carlosgj94/rapid-reader/crates/domain/src/reader.rs

extern crate alloc;

use alloc::boxed::Box;

use crate::{
    content::{
        ArticleId, CONTENT_ID_MAX_BYTES, CONTENT_TITLE_MAX_BYTES, CollectionKind,
        PrepareContentProgress, REMOTE_ITEM_ID_MAX_BYTES, ReaderPauseDetail, ReadingProgressEntry,
        SOURCE_ID_MAX_BYTES,
    },
    formatter::{MAX_PARAGRAPH_PREVIEW_BYTES, ReadingDocument, ReadingUnit},
    settings::{DEFAULT_READING_SPEED_WPM, MIN_READING_SPEED_WPM, READING_SPEED_STEP_WPM},
    text::InlineText,
};

pub const READER_WINDOW_MAX_UNITS: usize = 128;
const READER_WINDOW_OVERLAP_UNITS: u32 = 32;
const READER_WINDOW_PREFETCH_THRESHOLD_UNITS: u32 = 24;
const SPEED_RAMP_DURATION_MS: u64 = 10_000;
const SPEED_RAMP_START_NUMERATOR: u16 = 2;
const SPEED_RAMP_START_DENOMINATOR: u16 = 3;
const SPEED_RAMP_IDLE_AT_MS: u64 = u64::MAX;
const SPEED_RAMP_PENDING_AT_MS: u64 = u64::MAX - 1;
const PREPARE_PROGRESS_PERMILLE_MAX: u16 = 1_000;
const PREPARE_PROGRESS_ANIMATION_MIN_STEP_PERMILLE: u16 = 28;
const PREPARE_PROGRESS_STRIPE_PHASES: u8 = 8;

const EMPTY_READER_WINDOW: ReaderWindow = ReaderWindow::empty();

#[derive(Debug, Clone, Copy, Eq, PartialEq, Default)]
pub enum ReaderMode {
    #[default]
    Normal,
    Chat,
    Paused,
    ParagraphNavigation,
    LoadingContent,
}

#[derive(Debug, Clone, Copy, Eq, PartialEq, Default)]
pub enum PauseMenuRow {
    #[default]
    ResumeRsvp,
    ParagraphView,
    SaveArticle,
    Subscription,
}

impl PauseMenuRow {
    pub fn previous(self) -> Self {
        match self {
            Self::ResumeRsvp => Self::ResumeRsvp,
            Self::ParagraphView => Self::ResumeRsvp,
            Self::SaveArticle => Self::ParagraphView,
            Self::Subscription => Self::SaveArticle,
        }
    }

    pub fn next(self) -> Self {
        match self {
            Self::ResumeRsvp => Self::ParagraphView,
            Self::ParagraphView => Self::SaveArticle,
            Self::SaveArticle => Self::Subscription,
            Self::Subscription => Self::Subscription,
        }
    }
}

#[derive(Debug, Clone, Copy, Eq, PartialEq, Default)]
pub enum ReaderPauseMetadataStatus {
    #[default]
    Uninitialized,
    Loading,
    Ready,
    Failed,
}

#[derive(Debug, Clone, Copy, Eq, PartialEq, Default)]
pub enum ReaderPausePendingAction {
    #[default]
    None,
    Save,
    Subscription,
}

#[derive(Debug, Clone, Copy, Eq, PartialEq, Default)]
pub enum ReaderPauseActionError {
    #[default]
    None,
    Save,
    Subscription,
}

#[derive(Debug, Clone, Copy, Eq, PartialEq)]
pub enum ReaderPauseActionKind {
    Save,
    Subscription,
}

#[derive(Debug, Clone, Copy, Eq, PartialEq)]
pub struct ReaderPauseState {
    pub selected_row: PauseMenuRow,
    pub metadata_status: ReaderPauseMetadataStatus,
    pub pending_action: ReaderPausePendingAction,
    pub action_error: ReaderPauseActionError,
    pub is_saved: bool,
    pub is_subscribed_source: bool,
    pub saved_content_id: InlineText<REMOTE_ITEM_ID_MAX_BYTES>,
    pub source_id: InlineText<SOURCE_ID_MAX_BYTES>,
}

impl ReaderPauseState {
    pub const fn new() -> Self {
        Self {
            selected_row: PauseMenuRow::ResumeRsvp,
            metadata_status: ReaderPauseMetadataStatus::Uninitialized,
            pending_action: ReaderPausePendingAction::None,
            action_error: ReaderPauseActionError::None,
            is_saved: false,
            is_subscribed_source: false,
            saved_content_id: InlineText::new(),
            source_id: InlineText::new(),
        }
    }

    pub fn clear(&mut self) {
        *self = Self::new();
    }
}

impl Default for ReaderPauseState {
    fn default() -> Self {
        Self::new()
    }
}

#[derive(Debug, Clone, Copy, Eq, PartialEq, Default)]
pub struct ReaderProgress {
    pub unit_index: u32,
    pub paragraph_index: u16,
    pub total_paragraphs: u16,
    pub completion_percent: u8,
}

#[derive(Debug, Clone, Copy, Eq, PartialEq, Default)]
pub struct ReaderParagraphInfo {
    pub start_unit_index: u32,
    pub preview: InlineText<MAX_PARAGRAPH_PREVIEW_BYTES>,
}

#[derive(Debug, Clone, Eq, PartialEq)]
pub struct ReaderWindow {
    pub start_unit_index: u32,
    pub unit_count: u16,
    pub units: [ReadingUnit; READER_WINDOW_MAX_UNITS],
}

#[derive(Debug, Clone, Copy, Eq, PartialEq)]
pub struct ReaderWindowLoadRequest {
    pub content_id: InlineText<CONTENT_ID_MAX_BYTES>,
    pub window_start_unit_index: u32,
}

#[derive(Debug, Clone, Copy, Eq, PartialEq, Default)]
pub struct ReaderAdvanceOutcome {
    pub advanced: bool,
    pub load_request: Option<ReaderWindowLoadRequest>,
}

#[derive(Debug, Clone)]
pub struct ReaderSession {
    pub active_article: ArticleId,
    pub active_collection: CollectionKind,
    pub active_content_id: InlineText<CONTENT_ID_MAX_BYTES>,
    pub active_remote_revision: u64,
    pub title: InlineText<CONTENT_TITLE_MAX_BYTES>,
    active_window: Option<Box<ReaderWindow>>,
    prefetched_window: Option<Box<ReaderWindow>>,
    paragraphs: Option<Box<[ReaderParagraphInfo]>>,
    total_units: u32,
    pending_window_start_unit_index: Option<u32>,
    pending_seek_unit_index: Option<u32>,
    pub progress: ReaderProgress,
    pub mode: ReaderMode,
    pub resume_mode: ReaderMode,
    pub chat_available: bool,
    pub next_due_at_ms: Option<u64>,
    pub effective_wpm: u16,
    pub pause: ReaderPauseState,
    speed_ramp_start_wpm: u16,
    speed_ramp_started_at_ms: u64,
    prepare_progress: PrepareContentProgress,
    prepare_display_progress_permille: u16,
    prepare_stripe_phase: u8,
}

impl ReaderWindow {
    pub const fn empty() -> Self {
        Self {
            start_unit_index: 0,
            unit_count: 0,
            units: [ReadingUnit::new(); READER_WINDOW_MAX_UNITS],
        }
    }

    pub const fn is_empty(&self) -> bool {
        self.unit_count == 0
    }

    pub fn contains(&self, global_unit_index: u32) -> bool {
        !self.is_empty()
            && global_unit_index >= self.start_unit_index
            && global_unit_index < self.start_unit_index.saturating_add(self.unit_count as u32)
    }

    pub fn unit_at(&self, global_unit_index: u32) -> &ReadingUnit {
        if self.is_empty() {
            return &self.units[0];
        }

        let relative = global_unit_index
            .saturating_sub(self.start_unit_index)
            .min(self.unit_count.saturating_sub(1) as u32) as usize;
        &self.units[relative]
    }
}

impl ReaderSession {
    pub fn new() -> Self {
        Self {
            active_article: ArticleId(102),
            active_collection: CollectionKind::Saved,
            active_content_id: InlineText::new(),
            active_remote_revision: 0,
            title: InlineText::new(),
            active_window: None,
            prefetched_window: None,
            paragraphs: None,
            total_units: 0,
            pending_window_start_unit_index: None,
            pending_seek_unit_index: None,
            progress: ReaderProgress {
                unit_index: 0,
                paragraph_index: 1,
                total_paragraphs: 1,
                completion_percent: 0,
            },
            mode: ReaderMode::Normal,
            resume_mode: ReaderMode::Normal,
            chat_available: true,
            next_due_at_ms: None,
            effective_wpm: DEFAULT_READING_SPEED_WPM,
            pause: ReaderPauseState::new(),
            speed_ramp_start_wpm: 0,
            speed_ramp_started_at_ms: SPEED_RAMP_IDLE_AT_MS,
            prepare_progress: PrepareContentProgress::connecting(),
            prepare_display_progress_permille: 0,
            prepare_stripe_phase: 0,
        }
    }

    pub fn begin_content_loading(
        &mut self,
        collection: CollectionKind,
        content_id: InlineText<CONTENT_ID_MAX_BYTES>,
        title: InlineText<CONTENT_TITLE_MAX_BYTES>,
    ) {
        self.active_collection = collection;
        self.active_content_id = content_id;
        self.active_remote_revision = 0;
        self.title = title;
        self.active_window = None;
        self.prefetched_window = None;
        self.paragraphs = None;
        self.total_units = 0;
        self.pending_window_start_unit_index = None;
        self.pending_seek_unit_index = None;
        self.progress = ReaderProgress {
            unit_index: 0,
            paragraph_index: 1,
            total_paragraphs: 1,
            completion_percent: 0,
        };
        self.mode = ReaderMode::LoadingContent;
        self.resume_mode = ReaderMode::Normal;
        self.chat_available = false;
        self.next_due_at_ms = None;
        self.prepare_progress = PrepareContentProgress::connecting();
        self.prepare_display_progress_permille = 0;
        self.prepare_stripe_phase = 0;
        self.pause.clear();
        self.clear_speed_ramp();
        self.effective_wpm = DEFAULT_READING_SPEED_WPM;
    }

    pub fn open_article(
        &mut self,
        collection: CollectionKind,
        article: ArticleId,
        title: InlineText<CONTENT_TITLE_MAX_BYTES>,
        document: Box<ReadingDocument>,
        chat_available: bool,
        target_wpm: u16,
    ) {
        let paragraph_count = document.paragraph_count as usize;
        let mut paragraphs = alloc::vec::Vec::with_capacity(paragraph_count);
        let mut paragraph_index = 0usize;
        while paragraph_index < paragraph_count {
            paragraphs.push(ReaderParagraphInfo {
                start_unit_index: document.paragraphs[paragraph_index].start_unit_index as u32,
                preview: document.paragraphs[paragraph_index].preview,
            });
            paragraph_index += 1;
        }

        let mut window = Box::new(ReaderWindow::empty());
        let unit_count = document.unit_count.min(READER_WINDOW_MAX_UNITS as u16);
        let mut unit_index = 0usize;
        while unit_index < unit_count as usize {
            window.units[unit_index] = document.units[unit_index];
            unit_index += 1;
        }
        window.unit_count = unit_count;

        let _ = self.open_cached_reader_content(
            collection,
            article,
            InlineText::new(),
            0,
            title,
            document.unit_count as u32,
            paragraphs.into_boxed_slice(),
            window,
            chat_available,
            target_wpm,
            None,
        );
    }

    #[allow(clippy::too_many_arguments)]
    pub fn open_cached_reader_content(
        &mut self,
        collection: CollectionKind,
        article: ArticleId,
        content_id: InlineText<CONTENT_ID_MAX_BYTES>,
        remote_revision: u64,
        title: InlineText<CONTENT_TITLE_MAX_BYTES>,
        total_units: u32,
        paragraphs: Box<[ReaderParagraphInfo]>,
        window: Box<ReaderWindow>,
        chat_available: bool,
        target_wpm: u16,
        resume_paragraph_index: Option<u16>,
    ) -> Option<ReaderWindowLoadRequest> {
        self.active_collection = collection;
        self.active_article = article;
        self.active_content_id = content_id;
        self.active_remote_revision = remote_revision;
        self.title = title;
        self.total_units = total_units;
        self.paragraphs = Some(paragraphs);
        self.active_window = Some(window);
        self.prefetched_window = None;
        self.pending_window_start_unit_index = None;
        self.pending_seek_unit_index = None;
        self.progress.unit_index = 0;
        self.sync_progress();
        self.mode = ReaderMode::Normal;
        self.resume_mode = ReaderMode::Normal;
        self.chat_available = chat_available;
        self.next_due_at_ms = None;
        self.prepare_progress = PrepareContentProgress::connecting();
        self.prepare_display_progress_permille = 0;
        self.prepare_stripe_phase = 0;
        self.pause.clear();
        let request = resume_paragraph_index.and_then(|paragraph_index| {
            self.seek_to_unit(self.paragraph_start(paragraph_index.max(1)), target_wpm)
        });
        if self.pending_seek_unit_index.is_none() && self.progress.unit_index == 0 {
            self.arm_speed_ramp(target_wpm);
        }
        request
    }

    pub fn apply_loaded_window(&mut self, window: Box<ReaderWindow>) {
        let pending_seek = self.pending_seek_unit_index;
        self.pending_window_start_unit_index = None;

        if let Some(target_unit_index) = pending_seek
            && window.contains(target_unit_index)
        {
            Self::write_window_slot(&mut self.active_window, window);
            self.prefetched_window = None;
            self.pending_seek_unit_index = None;
            self.progress.unit_index = target_unit_index;
            self.sync_progress();
            self.next_due_at_ms = None;
            return;
        }

        let replace_active = self.active_window.as_ref().is_none_or(|active| {
            active.is_empty() || window.start_unit_index <= active.start_unit_index
        });

        if replace_active {
            Self::write_window_slot(&mut self.active_window, window);
            self.sync_progress();
        } else {
            Self::write_window_slot(&mut self.prefetched_window, window);
        }
    }

    pub fn unload_document(&mut self) {
        self.active_content_id = InlineText::new();
        self.active_remote_revision = 0;
        self.active_window = None;
        self.prefetched_window = None;
        self.paragraphs = None;
        self.total_units = 0;
        self.pending_window_start_unit_index = None;
        self.pending_seek_unit_index = None;
        self.progress = ReaderProgress {
            unit_index: 0,
            paragraph_index: 1,
            total_paragraphs: 1,
            completion_percent: 0,
        };
        self.mode = ReaderMode::Normal;
        self.resume_mode = ReaderMode::Normal;
        self.next_due_at_ms = None;
        self.clear_speed_ramp();
        self.effective_wpm = DEFAULT_READING_SPEED_WPM;
        self.prepare_progress = PrepareContentProgress::connecting();
        self.prepare_display_progress_permille = 0;
        self.prepare_stripe_phase = 0;
        self.pause.clear();
    }

    pub fn clear_pending_window_request(&mut self) {
        let had_pending_seek = self.pending_seek_unit_index.is_some();
        self.pending_window_start_unit_index = None;
        self.pending_seek_unit_index = None;
        self.prefetched_window = None;
        self.next_due_at_ms = None;
        if had_pending_seek {
            self.clear_speed_ramp();
        }
    }

    pub fn show_normal(&mut self) {
        if matches!(self.mode, ReaderMode::Normal | ReaderMode::Chat) {
            self.mode = ReaderMode::Normal;
            self.resume_mode = ReaderMode::Normal;
        }
    }

    pub fn show_chat(&mut self) {
        if self.chat_available && matches!(self.mode, ReaderMode::Normal | ReaderMode::Chat) {
            self.mode = ReaderMode::Chat;
            self.resume_mode = ReaderMode::Chat;
        }
    }

    pub fn pause(&mut self, seeded_is_saved: bool) {
        if matches!(self.mode, ReaderMode::Normal | ReaderMode::Chat) {
            self.resume_mode = self.mode;
            self.mode = ReaderMode::Paused;
            self.next_due_at_ms = None;
            self.clear_speed_ramp();
            self.pause.selected_row = PauseMenuRow::ResumeRsvp;
            if !matches!(self.pause.metadata_status, ReaderPauseMetadataStatus::Ready)
                && !matches!(self.pause.pending_action, ReaderPausePendingAction::Save)
            {
                self.pause.is_saved = seeded_is_saved;
            }
        }
    }

    pub fn resume(&mut self, target_wpm: u16) {
        if matches!(self.mode, ReaderMode::Paused) {
            self.mode = self.resume_mode;
            self.next_due_at_ms = None;
            self.arm_speed_ramp(target_wpm);
        }
    }

    pub fn open_paragraph_navigation(&mut self) {
        if matches!(self.mode, ReaderMode::Paused) {
            self.mode = ReaderMode::ParagraphNavigation;
            self.next_due_at_ms = None;
        }
    }

    pub fn close_paragraph_navigation(&mut self) {
        if matches!(self.mode, ReaderMode::ParagraphNavigation) {
            self.mode = ReaderMode::Paused;
        }
    }

    pub fn move_pause_selection(&mut self, previous: bool) {
        if !matches!(self.mode, ReaderMode::Paused) {
            return;
        }

        self.pause.selected_row = if previous {
            self.pause.selected_row.previous()
        } else {
            self.pause.selected_row.next()
        };
    }

    pub const fn selected_pause_row(&self) -> PauseMenuRow {
        self.pause.selected_row
    }

    pub const fn pause_needs_detail_load(&self) -> bool {
        matches!(self.mode, ReaderMode::Paused)
            && !self.active_content_id.is_empty()
            && matches!(
                self.pause.metadata_status,
                ReaderPauseMetadataStatus::Uninitialized | ReaderPauseMetadataStatus::Failed
            )
            && matches!(self.pause.pending_action, ReaderPausePendingAction::None)
    }

    pub fn begin_pause_detail_load(&mut self) {
        if self.active_content_id.is_empty() {
            return;
        }

        self.pause.metadata_status = ReaderPauseMetadataStatus::Loading;
        self.pause.action_error = ReaderPauseActionError::None;
    }

    pub fn apply_pause_detail(&mut self, detail: ReaderPauseDetail) {
        if self.active_content_id != detail.content_id {
            return;
        }

        self.pause.metadata_status = ReaderPauseMetadataStatus::Ready;
        self.pause.pending_action = ReaderPausePendingAction::None;
        self.pause.action_error = ReaderPauseActionError::None;
        self.pause.is_saved = detail.is_saved;
        self.pause.is_subscribed_source = detail.is_subscribed_source;
        self.pause.saved_content_id = detail.saved_content_id;
        self.pause.source_id = detail.source_id;
    }

    pub fn mark_pause_detail_failed(&mut self, content_id: InlineText<CONTENT_ID_MAX_BYTES>) {
        if self.active_content_id != content_id {
            return;
        }

        if !matches!(self.pause.pending_action, ReaderPausePendingAction::None) {
            return;
        }

        self.pause.metadata_status = ReaderPauseMetadataStatus::Failed;
    }

    pub fn begin_pause_save_toggle(&mut self) {
        self.pause.pending_action = ReaderPausePendingAction::Save;
        if matches!(self.pause.action_error, ReaderPauseActionError::Save) {
            self.pause.action_error = ReaderPauseActionError::None;
        }
    }

    pub fn begin_pause_subscription_toggle(&mut self) {
        self.pause.pending_action = ReaderPausePendingAction::Subscription;
        if matches!(
            self.pause.action_error,
            ReaderPauseActionError::Subscription
        ) {
            self.pause.action_error = ReaderPauseActionError::None;
        }
    }

    pub fn apply_pause_action(
        &mut self,
        content_id: InlineText<CONTENT_ID_MAX_BYTES>,
        action: ReaderPauseActionKind,
        enabled: bool,
    ) {
        if self.active_content_id != content_id {
            return;
        }

        match action {
            ReaderPauseActionKind::Save => {
                self.pause.pending_action = ReaderPausePendingAction::None;
                self.pause.action_error = ReaderPauseActionError::None;
                self.pause.is_saved = enabled;
            }
            ReaderPauseActionKind::Subscription => {
                self.pause.pending_action = ReaderPausePendingAction::None;
                self.pause.action_error = ReaderPauseActionError::None;
                self.pause.is_subscribed_source = enabled;
            }
        }
    }

    pub fn fail_pause_action(
        &mut self,
        content_id: InlineText<CONTENT_ID_MAX_BYTES>,
        action: ReaderPauseActionKind,
    ) {
        if self.active_content_id != content_id {
            return;
        }

        match action {
            ReaderPauseActionKind::Save => {
                self.pause.pending_action = ReaderPausePendingAction::None;
                self.pause.action_error = ReaderPauseActionError::Save;
            }
            ReaderPauseActionKind::Subscription => {
                self.pause.pending_action = ReaderPausePendingAction::None;
                self.pause.action_error = ReaderPauseActionError::Subscription;
            }
        }
    }

    pub fn commit_paragraph_navigation(
        &mut self,
        target_wpm: u16,
    ) -> Option<ReaderWindowLoadRequest> {
        if !matches!(self.mode, ReaderMode::ParagraphNavigation) {
            return None;
        }

        self.mode = self.resume_mode;
        self.seek_to_unit(
            self.paragraph_start(self.progress.paragraph_index),
            target_wpm,
        )
    }

    pub fn move_paragraph(&mut self, previous: bool) {
        let min_paragraph = 1u16;
        let max_paragraph = self.progress.total_paragraphs.max(1);

        self.progress.paragraph_index = if previous {
            self.progress
                .paragraph_index
                .saturating_sub(1)
                .max(min_paragraph)
        } else {
            self.progress
                .paragraph_index
                .saturating_add(1)
                .min(max_paragraph)
        };
    }

    pub fn jump_live_previous_paragraph(
        &mut self,
        target_wpm: u16,
    ) -> Option<ReaderWindowLoadRequest> {
        if !self.is_active_reading() {
            return None;
        }

        let current_start = self.paragraph_start(self.progress.paragraph_index);
        if self.progress.unit_index > current_start {
            return self.seek_to_unit(current_start, target_wpm);
        }

        if self.progress.paragraph_index > 1 {
            return self.seek_to_unit(
                self.paragraph_start(self.progress.paragraph_index - 1),
                target_wpm,
            );
        }

        None
    }

    pub fn jump_live_next_paragraph(&mut self, target_wpm: u16) -> Option<ReaderWindowLoadRequest> {
        if !self.is_active_reading()
            || self.progress.paragraph_index >= self.progress.total_paragraphs.max(1)
        {
            return None;
        }

        self.seek_to_unit(
            self.paragraph_start(self.progress.paragraph_index + 1),
            target_wpm,
        )
    }

    pub const fn is_active_reading(&self) -> bool {
        matches!(self.mode, ReaderMode::Normal | ReaderMode::Chat)
    }

    pub fn advance_if_due(&mut self, now_ms: u64, wpm: u16) -> ReaderAdvanceOutcome {
        let mut outcome = ReaderAdvanceOutcome::default();
        if !self.is_active_reading() || self.active_window().is_empty() {
            return outcome;
        }

        if self.pending_seek_unit_index.is_some() {
            return outcome;
        }

        self.refresh_effective_wpm(now_ms, wpm);
        let current = self.current_unit();
        let next_due = self
            .next_due_at_ms
            .unwrap_or_else(|| now_ms.saturating_add(current.dwell_ms(self.effective_wpm) as u64));

        if self.next_due_at_ms.is_none() {
            self.next_due_at_ms = Some(next_due);
            outcome.load_request = self.maybe_request_prefetch();
            return outcome;
        }

        if now_ms < next_due {
            outcome.load_request = self.maybe_request_prefetch();
            return outcome;
        }

        if self.progress.unit_index.saturating_add(1) >= self.total_units.max(1) {
            self.next_due_at_ms = None;
            self.progress.completion_percent = 100;
            self.clear_speed_ramp();
            self.effective_wpm = wpm;
            return outcome;
        }

        let next_unit_index = self.progress.unit_index.saturating_add(1);
        if !self.active_window().contains(next_unit_index) {
            if self
                .prefetched_window
                .as_ref()
                .is_some_and(|window| window.contains(next_unit_index))
            {
                self.active_window = self.prefetched_window.take();
            } else {
                self.next_due_at_ms = None;
                outcome.load_request =
                    self.load_request_for_window_start(self.window_start_for_unit(next_unit_index));
                return outcome;
            }
        }

        self.progress.unit_index = next_unit_index;
        self.sync_progress();
        self.refresh_effective_wpm(now_ms, wpm);
        self.next_due_at_ms =
            Some(now_ms.saturating_add(self.current_unit().dwell_ms(self.effective_wpm) as u64));
        outcome.advanced = true;
        outcome.load_request = self.maybe_request_prefetch();
        outcome
    }

    pub fn display_wpm(&self, target_wpm: u16) -> u16 {
        if self.speed_ramp_started_at_ms == SPEED_RAMP_IDLE_AT_MS {
            target_wpm
        } else {
            quantize_display_wpm(self.effective_wpm, target_wpm)
        }
    }

    pub const fn prepare_progress(&self) -> PrepareContentProgress {
        self.prepare_progress
    }

    pub fn update_prepare_progress(&mut self, progress: PrepareContentProgress) {
        if matches!(self.mode, ReaderMode::LoadingContent) {
            self.prepare_progress = progress;
            let target = prepare_progress_permille(progress);
            if target < self.prepare_display_progress_permille {
                self.prepare_display_progress_permille = target;
            }
        }
    }

    pub fn advance_prepare_animation(&mut self) {
        if !matches!(self.mode, ReaderMode::LoadingContent) {
            self.prepare_display_progress_permille =
                prepare_progress_permille(self.prepare_progress);
            self.prepare_stripe_phase = 0;
            return;
        }

        self.prepare_stripe_phase =
            (self.prepare_stripe_phase + 1) % PREPARE_PROGRESS_STRIPE_PHASES.max(1);

        let target = prepare_progress_permille(self.prepare_progress);
        if self.prepare_display_progress_permille >= target {
            self.prepare_display_progress_permille = target;
            return;
        }

        let delta = target.saturating_sub(self.prepare_display_progress_permille);
        let eased_step = delta / 3;
        let step = if eased_step > PREPARE_PROGRESS_ANIMATION_MIN_STEP_PERMILLE {
            eased_step
        } else {
            PREPARE_PROGRESS_ANIMATION_MIN_STEP_PERMILLE
        };
        self.prepare_display_progress_permille = self
            .prepare_display_progress_permille
            .saturating_add(step)
            .min(target);
    }

    pub const fn prepare_display_progress_width_px(&self, max_width_px: u16) -> u16 {
        ((max_width_px as u32 * self.prepare_display_progress_permille as u32)
            / PREPARE_PROGRESS_PERMILLE_MAX as u32) as u16
    }

    pub const fn prepare_stripe_phase(&self) -> u8 {
        self.prepare_stripe_phase
    }

    pub fn current_unit(&self) -> &ReadingUnit {
        self.active_window().unit_at(self.progress.unit_index)
    }

    pub fn reading_progress_checkpoint(&self) -> Option<ReadingProgressEntry> {
        if self.active_content_id.is_empty()
            || matches!(self.mode, ReaderMode::LoadingContent)
            || self.active_window().is_empty()
        {
            return None;
        }

        Some(
            ReadingProgressEntry {
                content_id: self.active_content_id,
                remote_revision: self.active_remote_revision,
                paragraph_index: self.progress.paragraph_index.max(1),
                total_paragraphs: self.progress.total_paragraphs.max(1),
            }
            .sanitized(),
        )
    }

    pub fn preview_for_paragraph(
        &self,
        paragraph_index: u16,
    ) -> InlineText<MAX_PARAGRAPH_PREVIEW_BYTES> {
        self.paragraphs
            .as_deref()
            .and_then(|paragraphs| {
                if paragraphs.is_empty() {
                    return None;
                }

                let safe_index = paragraph_index
                    .saturating_sub(1)
                    .min(paragraphs.len().saturating_sub(1) as u16)
                    as usize;
                Some(paragraphs[safe_index].preview)
            })
            .or_else(|| Self::preview_from_window(self.active_window(), paragraph_index))
            .or_else(|| {
                self.prefetched_window
                    .as_deref()
                    .and_then(|window| Self::preview_from_window(window, paragraph_index))
            })
            .unwrap_or_default()
    }

    pub fn paragraph_start(&self, paragraph_index: u16) -> u32 {
        let Some(paragraphs) = self.paragraphs.as_deref() else {
            return 0;
        };
        let safe_index = paragraph_index
            .saturating_sub(1)
            .min(paragraphs.len().saturating_sub(1) as u16) as usize;
        paragraphs[safe_index].start_unit_index
    }

    pub fn active_window(&self) -> &ReaderWindow {
        self.active_window
            .as_deref()
            .unwrap_or(&EMPTY_READER_WINDOW)
    }

    pub const fn progress_width_px(&self) -> u16 {
        ((400u32 * self.progress.completion_percent as u32) / 100u32) as u16
    }

    pub fn is_empty(&self) -> bool {
        self.total_units == 0 || self.active_window().is_empty()
    }

    fn sync_progress(&mut self) {
        let total_paragraphs = self
            .paragraphs
            .as_deref()
            .map(|paragraphs| paragraphs.len() as u16)
            .unwrap_or(0)
            .max(1);
        self.progress.total_paragraphs = total_paragraphs;
        self.progress.paragraph_index = self.find_paragraph_for_unit(self.progress.unit_index);

        let total_units = self.total_units.max(1);
        let current = self.progress.unit_index.min(total_units.saturating_sub(1)) + 1;
        self.progress.completion_percent = ((current * 100) / total_units) as u8;
    }

    fn find_paragraph_for_unit(&self, unit_index: u32) -> u16 {
        let Some(paragraphs) = self.paragraphs.as_deref() else {
            return 1;
        };
        if paragraphs.is_empty() {
            return 1;
        }

        let mut low = 0usize;
        let mut high = paragraphs.len();
        while low + 1 < high {
            let mid = (low + high) / 2;
            if paragraphs[mid].start_unit_index <= unit_index {
                low = mid;
            } else {
                high = mid;
            }
        }

        (low + 1) as u16
    }

    fn maybe_request_prefetch(&mut self) -> Option<ReaderWindowLoadRequest> {
        if self.active_content_id.is_empty()
            || self.prefetched_window.is_some()
            || self.pending_window_start_unit_index.is_some()
            || self.total_units == 0
        {
            return None;
        }

        let active = self.active_window();
        if active.is_empty() {
            return None;
        }

        let window_end = active
            .start_unit_index
            .saturating_add(active.unit_count as u32);
        if window_end >= self.total_units {
            return None;
        }

        let remaining_in_window =
            window_end.saturating_sub(self.progress.unit_index.saturating_add(1));
        if remaining_in_window > READER_WINDOW_PREFETCH_THRESHOLD_UNITS {
            return None;
        }

        let next_start = active
            .start_unit_index
            .saturating_add(active.unit_count as u32)
            .saturating_sub(READER_WINDOW_OVERLAP_UNITS);
        self.load_request_for_window_start(next_start)
    }

    fn load_request_for_window_start(
        &mut self,
        window_start_unit_index: u32,
    ) -> Option<ReaderWindowLoadRequest> {
        if self.active_content_id.is_empty() {
            return None;
        }

        let clamped_start = window_start_unit_index.min(self.total_units.saturating_sub(1));
        if self.pending_window_start_unit_index == Some(clamped_start)
            || self.active_window().start_unit_index == clamped_start
            || self
                .prefetched_window
                .as_ref()
                .is_some_and(|window| window.start_unit_index == clamped_start)
        {
            return None;
        }

        self.pending_window_start_unit_index = Some(clamped_start);
        Some(ReaderWindowLoadRequest {
            content_id: self.active_content_id,
            window_start_unit_index: clamped_start,
        })
    }

    fn seek_to_unit(
        &mut self,
        target_unit_index: u32,
        target_wpm: u16,
    ) -> Option<ReaderWindowLoadRequest> {
        if self.total_units == 0 {
            return None;
        }

        let target_unit_index = target_unit_index.min(self.total_units.saturating_sub(1));
        if target_unit_index == self.progress.unit_index {
            return None;
        }

        self.next_due_at_ms = None;

        if self.active_window().contains(target_unit_index) {
            self.pending_seek_unit_index = None;
            self.progress.unit_index = target_unit_index;
            self.sync_progress();
            self.arm_speed_ramp(target_wpm);
            return None;
        }

        if self
            .prefetched_window
            .as_ref()
            .is_some_and(|window| window.contains(target_unit_index))
        {
            self.active_window = self.prefetched_window.take();
            self.pending_seek_unit_index = None;
            self.progress.unit_index = target_unit_index;
            self.sync_progress();
            self.arm_speed_ramp(target_wpm);
            return None;
        }

        self.pending_seek_unit_index = Some(target_unit_index);
        let request =
            self.load_request_for_window_start(self.window_start_for_unit(target_unit_index));
        if request.is_some() {
            self.arm_speed_ramp(target_wpm);
        } else {
            self.pending_seek_unit_index = None;
        }
        request
    }

    fn window_start_for_unit(&self, unit_index: u32) -> u32 {
        unit_index.saturating_sub(READER_WINDOW_OVERLAP_UNITS)
    }

    fn preview_from_window(
        window: &ReaderWindow,
        paragraph_index: u16,
    ) -> Option<InlineText<MAX_PARAGRAPH_PREVIEW_BYTES>> {
        if window.is_empty() {
            return None;
        }

        let target = paragraph_index.min(u8::MAX as u16) as u8;
        let mut preview = InlineText::new();
        let mut found = false;
        let mut unit_index = 0usize;
        while unit_index < window.unit_count as usize {
            let unit = &window.units[unit_index];
            if unit.paragraph_index < target {
                unit_index += 1;
                continue;
            }
            if unit.paragraph_index > target {
                break;
            }

            if found {
                let _ = preview.try_push_char(' ');
            }
            let _ = preview.try_push_str(unit.display.as_str());
            found = true;

            if unit.flags.paragraph_end {
                break;
            }
            unit_index += 1;
        }

        found.then_some(preview)
    }

    fn write_window_slot(slot: &mut Option<Box<ReaderWindow>>, window: Box<ReaderWindow>) {
        if let Some(existing) = slot.as_mut() {
            **existing = *window;
        } else {
            *slot = Some(window);
        }
    }

    fn arm_speed_ramp(&mut self, target_wpm: u16) {
        let start_wpm = ramp_start_wpm(target_wpm);
        self.next_due_at_ms = None;
        self.speed_ramp_start_wpm = start_wpm;
        self.effective_wpm = start_wpm;
        self.speed_ramp_started_at_ms = if start_wpm < target_wpm {
            SPEED_RAMP_PENDING_AT_MS
        } else {
            SPEED_RAMP_IDLE_AT_MS
        };
    }

    fn clear_speed_ramp(&mut self) {
        self.speed_ramp_start_wpm = 0;
        self.speed_ramp_started_at_ms = SPEED_RAMP_IDLE_AT_MS;
    }

    fn refresh_effective_wpm(&mut self, now_ms: u64, target_wpm: u16) {
        match self.speed_ramp_started_at_ms {
            SPEED_RAMP_IDLE_AT_MS => {
                self.effective_wpm = target_wpm;
            }
            SPEED_RAMP_PENDING_AT_MS => {
                self.speed_ramp_started_at_ms = now_ms;
                self.effective_wpm = self.speed_ramp_start_wpm;
            }
            started_at_ms => {
                let elapsed_ms = now_ms.saturating_sub(started_at_ms);
                if elapsed_ms >= SPEED_RAMP_DURATION_MS || self.speed_ramp_start_wpm >= target_wpm {
                    self.clear_speed_ramp();
                    self.effective_wpm = target_wpm;
                    return;
                }

                let delta_wpm = target_wpm.saturating_sub(self.speed_ramp_start_wpm) as u64;
                let ramped_delta = (delta_wpm.saturating_mul(elapsed_ms)) / SPEED_RAMP_DURATION_MS;
                self.effective_wpm = self
                    .speed_ramp_start_wpm
                    .saturating_add(ramped_delta as u16)
                    .min(target_wpm);
            }
        }
    }
}

const fn ramp_start_wpm(target_wpm: u16) -> u16 {
    let scaled = ((target_wpm as u32 * SPEED_RAMP_START_NUMERATOR as u32)
        / SPEED_RAMP_START_DENOMINATOR as u32) as u16;
    if scaled < MIN_READING_SPEED_WPM {
        if MIN_READING_SPEED_WPM < target_wpm {
            MIN_READING_SPEED_WPM
        } else {
            target_wpm
        }
    } else if scaled < target_wpm {
        scaled
    } else {
        target_wpm
    }
}

const fn quantize_display_wpm(wpm: u16, target_wpm: u16) -> u16 {
    let clamped = if wpm < MIN_READING_SPEED_WPM {
        MIN_READING_SPEED_WPM
    } else if wpm > target_wpm {
        target_wpm
    } else {
        wpm
    };

    let steps = clamped.saturating_sub(MIN_READING_SPEED_WPM) / READING_SPEED_STEP_WPM;
    let quantized = MIN_READING_SPEED_WPM + (steps * READING_SPEED_STEP_WPM);
    if quantized < target_wpm {
        quantized
    } else {
        target_wpm
    }
}

const fn prepare_progress_permille(progress: PrepareContentProgress) -> u16 {
    if progress.total_steps == 0 {
        return 0;
    }

    let completed_steps = if progress.completed_steps > progress.total_steps {
        progress.total_steps
    } else {
        progress.completed_steps
    };

    ((completed_steps as u32 * PREPARE_PROGRESS_PERMILLE_MAX as u32) / progress.total_steps as u32)
        as u16
}

impl Default for ReaderSession {
    fn default() -> Self {
        Self::new()
    }
}

#[cfg(test)]
mod tests {
    use super::*;
    use crate::{
        content::{ArticleDocument, ReaderScript},
        formatter::format_article_document,
        source::SourceKind,
    };

    fn make_test_window(start_unit_index: u32, unit_count: u16) -> ReaderWindow {
        let mut window = ReaderWindow::empty();
        window.start_unit_index = start_unit_index;
        window.unit_count = unit_count;
        window
    }

    fn make_seekable_session(
        active_start_unit_index: u32,
        active_unit_count: u16,
        paragraph_starts: &[u32],
    ) -> ReaderSession {
        let mut session = ReaderSession::new();
        session.active_content_id = InlineText::from_slice("content-1");
        session.total_units = 400;
        session.progress.total_paragraphs = paragraph_starts.len() as u16;
        session.paragraphs = Some(
            paragraph_starts
                .iter()
                .copied()
                .map(|start_unit_index| ReaderParagraphInfo {
                    start_unit_index,
                    preview: InlineText::new(),
                })
                .collect::<alloc::vec::Vec<_>>()
                .into_boxed_slice(),
        );
        session.active_window = Some(Box::new(make_test_window(
            active_start_unit_index,
            active_unit_count,
        )));
        session
    }

    #[test]
    fn built_in_document_opens_inside_windowed_reader() {
        let document = format_article_document(&ArticleDocument::new(
            SourceKind::Unknown,
            ReaderScript::MachineSoul,
        ));
        let mut session = ReaderSession::new();

        session.open_article(
            CollectionKind::Saved,
            ArticleId(1),
            InlineText::from_slice("Example"),
            Box::new(document),
            false,
            300,
        );

        assert!(!session.is_empty());
        assert_eq!(session.progress.total_paragraphs, 8);
    }

    #[test]
    fn opening_article_arms_pending_speed_ramp() {
        let document = format_article_document(&ArticleDocument::new(
            SourceKind::Unknown,
            ReaderScript::MachineSoul,
        ));
        let mut session = ReaderSession::new();
        let start_wpm = ramp_start_wpm(300);

        session.open_article(
            CollectionKind::Saved,
            ArticleId(1),
            InlineText::from_slice("Example"),
            Box::new(document),
            false,
            300,
        );

        assert_eq!(session.display_wpm(300), start_wpm);
        assert_eq!(session.effective_wpm, start_wpm);
        assert_eq!(session.speed_ramp_started_at_ms, SPEED_RAMP_PENDING_AT_MS);
    }

    #[test]
    fn opening_cached_content_resumes_inside_loaded_window() {
        let mut session = ReaderSession::new();

        let request = session.open_cached_reader_content(
            CollectionKind::Saved,
            ArticleId(1),
            InlineText::from_slice("content-1"),
            7,
            InlineText::from_slice("Example"),
            300,
            alloc::vec![
                ReaderParagraphInfo {
                    start_unit_index: 0,
                    preview: InlineText::new(),
                },
                ReaderParagraphInfo {
                    start_unit_index: 64,
                    preview: InlineText::new(),
                },
                ReaderParagraphInfo {
                    start_unit_index: 128,
                    preview: InlineText::new(),
                },
            ]
            .into_boxed_slice(),
            Box::new(make_test_window(0, 128)),
            false,
            300,
            Some(2),
        );

        assert_eq!(request, None);
        assert_eq!(session.progress.unit_index, 64);
        assert_eq!(session.progress.paragraph_index, 2);
        assert_eq!(session.active_window().start_unit_index, 0);
    }

    #[test]
    fn opening_cached_content_requests_window_for_resume_outside_loaded_window() {
        let mut session = ReaderSession::new();
        let start_wpm = ramp_start_wpm(300);

        let request = session
            .open_cached_reader_content(
                CollectionKind::Saved,
                ArticleId(1),
                InlineText::from_slice("content-1"),
                7,
                InlineText::from_slice("Example"),
                300,
                alloc::vec![
                    ReaderParagraphInfo {
                        start_unit_index: 0,
                        preview: InlineText::new(),
                    },
                    ReaderParagraphInfo {
                        start_unit_index: 64,
                        preview: InlineText::new(),
                    },
                    ReaderParagraphInfo {
                        start_unit_index: 128,
                        preview: InlineText::new(),
                    },
                ]
                .into_boxed_slice(),
                Box::new(make_test_window(0, 32)),
                false,
                300,
                Some(2),
            )
            .unwrap();

        assert_eq!(request.content_id.as_str(), "content-1");
        assert_eq!(request.window_start_unit_index, 32);
        assert_eq!(session.pending_seek_unit_index, Some(64));
        assert_eq!(session.progress.unit_index, 0);
        assert_eq!(session.progress.paragraph_index, 1);
        assert_eq!(session.display_wpm(300), start_wpm);
    }

    #[test]
    fn first_reader_tick_uses_ramp_start_wpm_for_initial_dwell() {
        let document = format_article_document(&ArticleDocument::new(
            SourceKind::Unknown,
            ReaderScript::MachineSoul,
        ));
        let mut session = ReaderSession::new();
        let start_wpm = ramp_start_wpm(300);

        session.open_article(
            CollectionKind::Saved,
            ArticleId(1),
            InlineText::from_slice("Example"),
            Box::new(document),
            false,
            300,
        );

        session.advance_if_due(0, 300);

        assert_eq!(
            session.next_due_at_ms,
            Some(session.current_unit().dwell_ms(start_wpm) as u64)
        );
        assert_eq!(session.display_wpm(300), start_wpm);
    }

    #[test]
    fn speed_ramp_reaches_target_after_duration() {
        let document = format_article_document(&ArticleDocument::new(
            SourceKind::Unknown,
            ReaderScript::MachineSoul,
        ));
        let mut session = ReaderSession::new();
        let start_wpm = ramp_start_wpm(300);

        session.open_article(
            CollectionKind::Saved,
            ArticleId(1),
            InlineText::from_slice("Example"),
            Box::new(document),
            false,
            300,
        );
        session.advance_if_due(0, 300);
        session.next_due_at_ms = Some(u64::MAX);

        session.advance_if_due(3_000, 300);
        assert_eq!(session.effective_wpm, 230);
        assert_eq!(session.display_wpm(300), 220);

        session.advance_if_due(10_000, 300);
        assert_eq!(session.display_wpm(300), 300);
        assert_eq!(session.speed_ramp_started_at_ms, SPEED_RAMP_IDLE_AT_MS);
    }

    #[test]
    fn resume_arms_fresh_speed_ramp() {
        let document = format_article_document(&ArticleDocument::new(
            SourceKind::Unknown,
            ReaderScript::MachineSoul,
        ));
        let mut session = ReaderSession::new();
        let start_wpm = ramp_start_wpm(300);

        session.open_article(
            CollectionKind::Saved,
            ArticleId(1),
            InlineText::from_slice("Example"),
            Box::new(document),
            false,
            300,
        );
        session.pause(false);

        assert_eq!(session.display_wpm(300), 300);

        session.resume(300);

        assert_eq!(session.display_wpm(300), start_wpm);
        assert_eq!(session.speed_ramp_started_at_ms, SPEED_RAMP_PENDING_AT_MS);
    }

    #[test]
    fn minimum_target_speed_does_not_ramp_below_floor() {
        let document = format_article_document(&ArticleDocument::new(
            SourceKind::Unknown,
            ReaderScript::MachineSoul,
        ));
        let mut session = ReaderSession::new();

        session.open_article(
            CollectionKind::Saved,
            ArticleId(1),
            InlineText::from_slice("Example"),
            Box::new(document),
            false,
            MIN_READING_SPEED_WPM,
        );

        assert_eq!(
            session.display_wpm(MIN_READING_SPEED_WPM),
            MIN_READING_SPEED_WPM
        );
        assert_eq!(session.speed_ramp_started_at_ms, SPEED_RAMP_IDLE_AT_MS);
    }

    #[test]
    fn window_contains_checks_global_indices() {
        let mut window = ReaderWindow::empty();
        window.start_unit_index = 32;
        window.unit_count = 4;

        assert!(!window.contains(31));
        assert!(window.contains(32));
        assert!(window.contains(35));
        assert!(!window.contains(36));
    }

    #[test]
    fn paragraph_lookup_uses_global_indices() {
        let mut session = ReaderSession::new();
        session.paragraphs = Some(
            alloc::vec![
                ReaderParagraphInfo {
                    start_unit_index: 0,
                    preview: InlineText::from_slice("first"),
                },
                ReaderParagraphInfo {
                    start_unit_index: 5,
                    preview: InlineText::from_slice("second"),
                },
                ReaderParagraphInfo {
                    start_unit_index: 9,
                    preview: InlineText::from_slice("third"),
                },
            ]
            .into_boxed_slice(),
        );

        assert_eq!(session.find_paragraph_for_unit(0), 1);
        assert_eq!(session.find_paragraph_for_unit(6), 2);
        assert_eq!(session.find_paragraph_for_unit(20), 3);
    }

    #[test]
    fn live_previous_jump_rewinds_to_current_paragraph_start() {
        let mut session = make_seekable_session(0, 32, &[0, 5, 10]);
        session.progress.unit_index = 7;
        session.next_due_at_ms = Some(500);
        session.sync_progress();

        let request = session.jump_live_previous_paragraph(300);

        assert_eq!(request, None);
        assert_eq!(session.progress.unit_index, 5);
        assert_eq!(session.progress.paragraph_index, 2);
        assert_eq!(session.next_due_at_ms, None);
    }

    #[test]
    fn paragraph_preview_uses_global_metadata_outside_loaded_window() {
        let mut session = make_seekable_session(0, 32, &[0, 64, 128]);
        session.paragraphs = Some(
            alloc::vec![
                ReaderParagraphInfo {
                    start_unit_index: 0,
                    preview: InlineText::from_slice("first preview"),
                },
                ReaderParagraphInfo {
                    start_unit_index: 64,
                    preview: InlineText::from_slice("second preview"),
                },
                ReaderParagraphInfo {
                    start_unit_index: 128,
                    preview: InlineText::from_slice("third preview"),
                },
            ]
            .into_boxed_slice(),
        );

        assert_eq!(session.preview_for_paragraph(3).as_str(), "third preview");
    }

    #[test]
    fn live_previous_jump_at_paragraph_start_moves_to_previous_paragraph() {
        let mut session = make_seekable_session(0, 32, &[0, 5, 10]);
        session.progress.unit_index = 5;
        session.sync_progress();

        let request = session.jump_live_previous_paragraph(300);

        assert_eq!(request, None);
        assert_eq!(session.progress.unit_index, 0);
        assert_eq!(session.progress.paragraph_index, 1);
    }

    #[test]
    fn live_previous_jump_at_first_paragraph_start_is_noop() {
        let mut session = make_seekable_session(0, 32, &[0, 5, 10]);
        session.next_due_at_ms = Some(750);
        session.sync_progress();

        let request = session.jump_live_previous_paragraph(300);

        assert_eq!(request, None);
        assert_eq!(session.progress.unit_index, 0);
        assert_eq!(session.progress.paragraph_index, 1);
        assert_eq!(session.next_due_at_ms, Some(750));
    }

    #[test]
    fn live_next_jump_requests_window_when_target_is_not_loaded() {
        let mut session = make_seekable_session(0, 32, &[0, 64, 128]);
        session.total_units = 300;
        session.sync_progress();
        let start_wpm = ramp_start_wpm(300);

        let request = session.jump_live_next_paragraph(300).unwrap();

        assert_eq!(request.window_start_unit_index, 32);
        assert_eq!(request.content_id.as_str(), "content-1");
        assert_eq!(session.pending_seek_unit_index, Some(64));
        assert_eq!(session.next_due_at_ms, None);
        assert_eq!(session.display_wpm(300), start_wpm);
    }

    #[test]
    fn live_jump_promotes_prefetched_window_when_target_is_already_loaded() {
        let mut session = make_seekable_session(0, 32, &[0, 64, 128]);
        session.total_units = 300;
        session.prefetched_window = Some(Box::new(make_test_window(32, 96)));
        session.sync_progress();
        let start_wpm = ramp_start_wpm(300);

        let request = session.jump_live_next_paragraph(300);

        assert_eq!(request, None);
        assert_eq!(session.active_window().start_unit_index, 32);
        assert_eq!(session.progress.unit_index, 64);
        assert_eq!(session.progress.paragraph_index, 2);
        assert!(session.prefetched_window.is_none());
        assert_eq!(session.display_wpm(300), start_wpm);
    }

    #[test]
    fn apply_loaded_window_completes_pending_live_jump() {
        let mut session = make_seekable_session(0, 32, &[0, 64, 128]);
        session.total_units = 300;
        let start_wpm = ramp_start_wpm(300);
        let request = session.jump_live_next_paragraph(300).unwrap();

        session.apply_loaded_window(Box::new(make_test_window(
            request.window_start_unit_index,
            128,
        )));

        assert_eq!(session.progress.unit_index, 64);
        assert_eq!(session.progress.paragraph_index, 2);
        assert_eq!(session.pending_seek_unit_index, None);
        assert_eq!(session.active_window().start_unit_index, 32);
        assert_eq!(session.display_wpm(300), start_wpm);
    }

    #[test]
    fn pending_live_jump_uses_ramp_start_wpm_after_window_load() {
        let mut session = make_seekable_session(0, 32, &[0, 64, 128]);
        session.total_units = 300;
        let start_wpm = ramp_start_wpm(300);
        let request = session.jump_live_next_paragraph(300).unwrap();

        session.apply_loaded_window(Box::new(make_test_window(
            request.window_start_unit_index,
            128,
        )));
        session.advance_if_due(0, 300);

        assert_eq!(
            session.next_due_at_ms,
            Some(session.current_unit().dwell_ms(start_wpm) as u64)
        );
    }

    #[test]
    fn pending_live_jump_does_not_advance_old_window_while_loading() {
        let mut session = make_seekable_session(0, 32, &[0, 64, 128]);
        session.total_units = 300;
        let _request = session.jump_live_next_paragraph(300).unwrap();

        let outcome = session.advance_if_due(1_000, 300);

        assert!(!outcome.advanced);
        assert_eq!(session.progress.unit_index, 0);
        assert_eq!(session.next_due_at_ms, None);
    }

    #[test]
    fn live_jump_preserves_chat_mode() {
        let mut session = make_seekable_session(0, 32, &[0, 5, 10]);
        session.progress.unit_index = 7;
        session.sync_progress();
        session.mode = ReaderMode::Chat;
        session.resume_mode = ReaderMode::Chat;
        let start_wpm = ramp_start_wpm(300);

        let request = session.jump_live_previous_paragraph(300);

        assert_eq!(request, None);
        assert_eq!(session.mode, ReaderMode::Chat);
        assert_eq!(session.resume_mode, ReaderMode::Chat);
        assert_eq!(session.progress.unit_index, 5);
        assert_eq!(session.display_wpm(300), start_wpm);
    }

    #[test]
    fn commit_navigation_requests_window_when_target_is_not_loaded() {
        let mut session = ReaderSession::new();
        session.active_content_id = InlineText::from_slice("content-1");
        session.total_units = 400;
        session.mode = ReaderMode::ParagraphNavigation;
        session.resume_mode = ReaderMode::Normal;
        let start_wpm = ramp_start_wpm(300);
        session.progress.paragraph_index = 10;
        session.progress.total_paragraphs = 10;
        session.paragraphs = Some(
            alloc::vec![
                ReaderParagraphInfo {
                    start_unit_index: 0,
                    preview: InlineText::new(),
                };
                10
            ]
            .into_boxed_slice(),
        );
        if let Some(paragraphs) = session.paragraphs.as_mut() {
            paragraphs[9].start_unit_index = 256;
        }
        session.active_window = Some(Box::new(ReaderWindow::empty()));

        let request = session.commit_paragraph_navigation(300).unwrap();

        assert_eq!(request.window_start_unit_index, 224);
        assert_eq!(request.content_id.as_str(), "content-1");
        assert_eq!(session.display_wpm(300), start_wpm);
    }

    #[test]
    fn commit_navigation_uses_prefetched_window_when_available() {
        let mut session = make_seekable_session(0, 32, &[0, 64, 128]);
        session.mode = ReaderMode::ParagraphNavigation;
        session.resume_mode = ReaderMode::Normal;
        session.progress.paragraph_index = 2;
        session.prefetched_window = Some(Box::new(make_test_window(32, 96)));
        let start_wpm = ramp_start_wpm(300);

        let request = session.commit_paragraph_navigation(300);

        assert_eq!(request, None);
        assert_eq!(session.mode, ReaderMode::Normal);
        assert_eq!(session.active_window().start_unit_index, 32);
        assert_eq!(session.progress.unit_index, 64);
        assert_eq!(session.progress.paragraph_index, 2);
        assert_eq!(session.display_wpm(300), start_wpm);
    }
}
