carlosgj94/rapid-reader/crates/platform-esp32s3/src/backend.rs

#![cfg_attr(
    not(all(
        feature = "telemetry-memtrace",
        feature = "telemetry-verbose-diagnostics"
    )),
    allow(unused_imports, unused_variables)
)]

extern crate alloc;

use alloc::boxed::Box;
use core::net::{IpAddr, Ipv4Addr};
use core::{ffi::CStr, fmt::Write as _, future::Future, mem::size_of, net::SocketAddr, str};

use embassy_executor::Spawner;
use embassy_futures::select::{Either, select};
use embassy_net::{
    Stack,
    dns::DnsSocket,
    tcp::client::{TcpClient, TcpClientState, TcpConnection},
};
use embassy_sync::{blocking_mutex::raw::CriticalSectionRawMutex, channel::Channel};
use embassy_time::{Duration, Instant, Timer, with_timeout};
use embedded_io as eio06;
use embedded_io_07 as eio07;
use embedded_io_async::{Read as AsyncRead06, Write as AsyncWrite06};
use embedded_io_async_07::{Read as AsyncRead07, Write as AsyncWrite07};
use embedded_nal_async::{AddrType, Dns as _, TcpConnect as _};
use esp_hal::{
    peripherals::{ADC1, RNG},
    rng::{Trng, TrngSource},
};
use log::{info, warn};
use mbedtls_rs::{
    Certificate, ClientSessionConfig, SerializedClientSession, Session, SessionConfig,
    SessionError, Tls, TlsReference, TlsVersion, X509,
};
use services::backend_sync::SyncStatus;
use services::storage::StorageError;

use crate::{
    bootstrap::{persist_backend_credential, publish_event},
    content_storage,
    storage::{BACKEND_REFRESH_TOKEN_MAX_LEN, BackendCredential},
    telemetry::{TraceContext, bool_flag, collection_label, next_request_id, next_sync_id},
    transfer_tuning,
};
use domain::{
    content::{
        CONTENT_META_MAX_BYTES, CONTENT_TITLE_MAX_BYTES, CollectionKind, CollectionManifestItem,
        CollectionManifestState, DetailLocator, MANIFEST_ITEM_CAPACITY, PackageState,
        PrepareContentPhase, PrepareContentProgress, PrepareContentRequest,
        RECOMMENDATION_SERVE_ID_MAX_BYTES, RECOMMENDATION_SUBTOPIC_CAPACITY,
        RECOMMENDATION_SUBTOPIC_LABEL_MAX_BYTES, RECOMMENDATION_SUBTOPIC_SLUG_MAX_BYTES,
        REMOTE_ITEM_ID_MAX_BYTES, ReaderPauseDetail, ReaderPauseDetailRequest,
        ReaderSavedToggleRequest, ReaderSubscriptionToggleRequest, RecommendationSubtopic,
        RecommendationSubtopicsState, RecommendationTopicRequest, RemoteContentStatus,
        SOURCE_ID_MAX_BYTES,
    },
    runtime::Event,
    text::InlineText,
};

pub(crate) const BACKEND_HOST: &str = "motif-backend-production-a143.up.railway.app";
const BACKEND_HOST_CSTR_BYTES: &[u8] = b"motif-backend-production-a143.up.railway.app\0";
const BACKEND_BASE_URL: &str = "https://motif-backend-production-a143.up.railway.app";
const HEALTH_PATH: &str = "/health";
const REFRESH_PATH: &str = "/device/v1/auth/session/refresh";
const ME_PATH: &str = "/device/v1/me";
const INBOX_PATH: &str = "/device/v1/me/inbox";
const SAVED_CONTENT_PATH: &str = "/device/v1/me/saved-content";
const RECOMMENDATIONS_PATH: &str = "/device/v1/me/recommendations/content";
const RECOMMENDATION_SUBTOPICS_PATH: &str = "/device/v1/me/recommendations/subtopics";
const RECOMMENDATION_TOPIC_PATH_PREFIX: &str = "/device/v1/me/recommendations/content/by-topic/";
const READER_PAUSE_CONTENT_PATH_PREFIX: &str = "/device/v1/me/content/";
const READER_SAVE_SUFFIX: &str = "/save";
const READER_SOURCE_SUBSCRIPTION_PATH_PREFIX: &str = "/device/v1/me/sources/";
const READER_SOURCE_SUBSCRIPTION_SUFFIX: &str = "/subscription";
pub(crate) const BACKEND_PORT: u16 = 443;
const NETWORK_POLL_MS: u64 = 500;
const RETRY_BACKOFF_MS: u64 = 10_000;
const TRANSPORT_RETRY_ATTEMPTS: usize = 2;
const PACKAGE_TRANSPORT_RETRY_ATTEMPTS: usize = 3;
const PACKAGE_RETRY_RECOVERY_ATTEMPTS: usize = 2;
const TRANSPORT_RETRY_BACKOFF_MS: u64 = 750;
const CONNECT_TIMEOUT_SECS: u64 = 5;
const AUTH_REFRESH_TLS_HANDSHAKE_TIMEOUT_SECS: u64 = 12;
const AUTH_REFRESH_IO_TIMEOUT_SECS: u64 = 12;
const AUTH_REFRESH_NETWORK_READY_TIMEOUT_SECS: u64 = 8;
const BUFFERED_METADATA_TLS_HANDSHAKE_TIMEOUT_SECS: u64 = 10;
const BUFFERED_METADATA_IO_TIMEOUT_SECS: u64 = 20;
const BUFFERED_METADATA_NETWORK_READY_TIMEOUT_SECS: u64 = 6;
const STREAMING_PACKAGE_TLS_HANDSHAKE_TIMEOUT_SECS: u64 = 12;
const STREAMING_PACKAGE_IO_TIMEOUT_SECS: u64 = 25;
const STREAMING_PACKAGE_NETWORK_READY_TIMEOUT_SECS: u64 = 12;
const PACKAGE_RETRY_NETWORK_READY_MAX_TIMEOUT_SECS: u64 = 30;
const REQUEST_NETWORK_READY_POLL_MS: u64 = 250;
// Real device traces showed that an aggressive background `/device/v1/me`
// keepalive could kill an otherwise healthy reusable TLS session between two
// article opens. Keep passive reuse for truly nearby follow-up requests, but
// apply a much stricter age limit to streaming package fetches because the
// server path was already resetting ~20 s idle package sockets on first write
// and even 10 s reuse windows were producing multi-second stalls before the
// next request reached first byte.
const REUSABLE_BUFFERED_SESSION_IDLE_TIMEOUT_SECS: u64 = 60;
const REUSABLE_STREAMING_SESSION_IDLE_TIMEOUT_SECS: u64 = 3;
const MBEDTLS_DEBUG_LEVEL: u32 = 0;
const STREAM_PROGRESS_LOG_INTERVAL_BYTES: usize = 16 * 1024;
const HTTP_RESPONSE_MAX_LEN: usize = 8 * 1024;
const HTTP_STREAM_HEADER_MAX_LEN: usize = 2048;
const COLLECTION_PAGE_LIMIT: usize = 4;
const COLLECTION_CURSOR_MAX_LEN: usize = 192;
const COLLECTION_PAGE_PATH_MAX_LEN: usize = 320;
const COLLECTION_FETCH_MAX_PAGES: usize = 32;
const STARTUP_SYNC_QUERY_COUNT: u8 = 4;
const REFRESH_BODY_OVERHEAD_LEN: usize = "{\"refresh_token\":\"\"}".len();
const REQUEST_BODY_MAX_LEN: usize = REFRESH_BODY_OVERHEAD_LEN + (BACKEND_REFRESH_TOKEN_MAX_LEN * 2);
const INBOX_LOG_PREVIEW_MAX_LEN: usize = 256;
const PACKAGE_DOWNLOAD_CHUNK_LEN: usize = transfer_tuning::PACKAGE_TRANSFER_CHUNK_LEN;
const PACKAGE_STORAGE_HANDOFF_CHUNK_LEN: usize =
    transfer_tuning::PACKAGE_TRANSFER_STORAGE_HANDOFF_CHUNK_LEN;
const PREPARE_PROGRESS_DOWNLOAD_STEP_BYTES: usize = 24 * 1024;
const PREPARE_PROGRESS_MIN_DOWNLOAD_STEPS: u16 = 3;
const PREPARE_PROGRESS_MAX_DOWNLOAD_STEPS: u16 = 8;
const PREPARE_PROGRESS_FIXED_STEPS: u16 = 3;
// Package prefetch materially increases boot-time latency and was timing out on
// real device/package responses. Keep startup focused on refresh + manifest sync.
const STARTUP_SAVED_PREFETCH_ENABLED: bool = false;
const STARTUP_SAVED_PREFETCH_LIMIT: usize = 1;
const USER_AGENT: &str = concat!(env!("CARGO_PKG_NAME"), "/", env!("CARGO_PKG_VERSION"));
const BACKEND_CA_CHAIN_PEM: &str =
    concat!(include_str!("../certs/letsencrypt_isrg_root_x1.pem"), "\0");
const BACKEND_CMD_QUEUE_CAPACITY: usize = 4;
// Large article fetches are now dominated by body transfer rather than SD or
// commit/open overhead. Widen only the receive side so the TCP window can hold
// more inbound package data without paying for a larger transmit buffer we do
// not meaningfully use on tiny GET/refresh requests.
const BACKEND_TCP_RX_BUFFER_LEN: usize = 16 * 1024;
const BACKEND_TCP_TX_BUFFER_LEN: usize = 4 * 1024;
type BackendTcpClientState =
    TcpClientState<1, BACKEND_TCP_RX_BUFFER_LEN, BACKEND_TCP_TX_BUFFER_LEN>;
type BackendTcpClient<'a> = TcpClient<'a, 1, BACKEND_TCP_RX_BUFFER_LEN, BACKEND_TCP_TX_BUFFER_LEN>;
type BackendTcpConnection<'a> =
    TcpConnection<'a, 1, BACKEND_TCP_RX_BUFFER_LEN, BACKEND_TCP_TX_BUFFER_LEN>;
type BackendTlsSession<'a> = Session<'a, CompatConnection<BackendTcpConnection<'a>>>;

static BACKEND_CMD_CH: Channel<
    CriticalSectionRawMutex,
    BackendCommand,
    BACKEND_CMD_QUEUE_CAPACITY,
> = Channel::new();

#[derive(Debug, Clone, Copy, Eq, PartialEq)]
pub enum CredentialSource {
    CompileTime,
    Stored,
}

impl CredentialSource {
    fn label(self) -> &'static str {
        match self {
            Self::CompileTime => "compile_time",
            Self::Stored => "stored",
        }
    }
}

#[derive(Debug, Clone, Copy, Eq, PartialEq)]
pub struct StartupCredential {
    pub credential: BackendCredential,
    pub source: CredentialSource,
}

#[derive(Debug, Clone, Copy, Eq, PartialEq)]
struct NetworkReady {
    address: embassy_net::Ipv4Cidr,
}

#[derive(Debug, Clone, Eq, PartialEq)]
struct RefreshSession {
    access_token: heapless::String<1536>,
    refresh_token: heapless::String<BACKEND_REFRESH_TOKEN_MAX_LEN>,
    expires_in: u64,
}

#[derive(Debug, Clone, Eq, PartialEq)]
struct ActiveAccessSession {
    access_token: heapless::String<1536>,
    valid_until_ms: u64,
}

impl ActiveAccessSession {
    fn from_refresh_session(session: &RefreshSession, now_ms: u64) -> Self {
        let ttl_ms = session.expires_in.saturating_mul(1000);
        let refresh_margin_ms = 60_000u64.min(ttl_ms.saturating_div(4));
        Self {
            access_token: session.access_token.clone(),
            valid_until_ms: now_ms.saturating_add(ttl_ms.saturating_sub(refresh_margin_ms)),
        }
    }

    fn is_valid_at(&self, now_ms: u64) -> bool {
        now_ms < self.valid_until_ms && !self.access_token.is_empty()
    }
}

#[derive(Debug, Clone, Eq, PartialEq)]
struct MeProfile {
    user_id: heapless::String<64>,
    role: heapless::String<32>,
}

#[derive(Debug, Clone, Eq, PartialEq)]
struct CollectionFetchSummary {
    trace: TraceContext,
    item_count: usize,
    next_cursor_present: bool,
    page_count: usize,
    body_bytes_total: usize,
    truncated_by_capacity: bool,
    body_preview: Option<heapless::String<INBOX_LOG_PREVIEW_MAX_LEN>>,
    body_preview_truncated: bool,
}

#[derive(Debug, Clone, Eq, PartialEq)]
struct CollectionFetchResult {
    summary: CollectionFetchSummary,
    collection: Box<CollectionManifestState>,
}

#[derive(Debug, Clone, Copy, Eq, PartialEq)]
enum CollectionEndpoint {
    Inbox,
    Saved,
    Recommendations,
}

impl CollectionEndpoint {
    const fn kind(self) -> CollectionKind {
        match self {
            Self::Inbox => CollectionKind::Inbox,
            Self::Saved => CollectionKind::Saved,
            Self::Recommendations => CollectionKind::Recommendations,
        }
    }

    const fn path(self) -> &'static str {
        match self {
            Self::Inbox => INBOX_PATH,
            Self::Saved => SAVED_CONTENT_PATH,
            Self::Recommendations => RECOMMENDATIONS_PATH,
        }
    }

    const fn extra_query(self) -> &'static str {
        match self {
            Self::Inbox => "",
            Self::Saved => "&archived=false",
            Self::Recommendations => "",
        }
    }

    const fn array_key(self) -> &'static str {
        match self {
            Self::Inbox => "\"inbox\"",
            Self::Saved | Self::Recommendations => "\"content\"",
        }
    }
}

fn empty_collection_state_box() -> Box<CollectionManifestState> {
    crate::memory_policy::external_or_global_box(CollectionManifestState::empty())
}

#[derive(Debug, Clone, Eq, PartialEq)]
struct CollectionFetchPage {
    collection: CollectionManifestState,
    next_cursor: Option<heapless::String<COLLECTION_CURSOR_MAX_LEN>>,
    body_preview: Option<heapless::String<INBOX_LOG_PREVIEW_MAX_LEN>>,
    body_preview_truncated: bool,
}

#[derive(Debug, Clone, Eq, PartialEq)]
struct CollectionFetchAccumulator {
    trace: TraceContext,
    collection: Box<CollectionManifestState>,
    page_count: usize,
    body_bytes_total: usize,
    next_cursor: Option<heapless::String<COLLECTION_CURSOR_MAX_LEN>>,
    truncated_by_capacity: bool,
    body_preview: Option<heapless::String<INBOX_LOG_PREVIEW_MAX_LEN>>,
    body_preview_truncated: bool,
}

impl CollectionFetchAccumulator {
    fn new(trace: TraceContext) -> Self {
        Self {
            trace,
            collection: empty_collection_state_box(),
            page_count: 0,
            body_bytes_total: 0,
            next_cursor: None,
            truncated_by_capacity: false,
            body_preview: None,
            body_preview_truncated: false,
        }
    }

    #[allow(clippy::too_many_arguments)]
    fn record_page(
        &mut self,
        endpoint: CollectionEndpoint,
        path: &str,
        body_bytes: usize,
        page_index: usize,
        page_item_count: usize,
        accepted_items: usize,
        next_cursor: Option<heapless::String<COLLECTION_CURSOR_MAX_LEN>>,
        body_preview: Option<heapless::String<INBOX_LOG_PREVIEW_MAX_LEN>>,
        body_preview_truncated: bool,
    ) {
        let next_cursor_present = next_cursor.is_some();
        let response_headroom = HTTP_RESPONSE_MAX_LEN.saturating_sub(body_bytes);

        self.page_count = self.page_count.saturating_add(1);
        self.body_bytes_total = self.body_bytes_total.saturating_add(body_bytes);

        if self.body_preview.is_none()
            && let Some(preview) = body_preview.as_ref()
        {
            self.body_preview = Some(preview.clone());
            self.body_preview_truncated = body_preview_truncated;
        }
        self.next_cursor = next_cursor;
        log_collection_fetch_page_metrics(
            self.trace,
            endpoint.kind(),
            path,
            page_index,
            body_bytes,
            page_item_count,
            accepted_items,
            next_cursor_present,
            response_headroom,
            self.collection.len(),
            self.truncated_by_capacity,
        );
    }

    fn should_continue(&self) -> bool {
        self.next_cursor.is_some()
            && !self.truncated_by_capacity
            && self.collection.len() < MANIFEST_ITEM_CAPACITY
            && self.page_count < COLLECTION_FETCH_MAX_PAGES
    }

    fn into_result(self) -> CollectionFetchResult {
        CollectionFetchResult {
            summary: CollectionFetchSummary {
                trace: self.trace,
                item_count: self.collection.len(),
                next_cursor_present: self.next_cursor.is_some() || self.truncated_by_capacity,
                page_count: self.page_count,
                body_bytes_total: self.body_bytes_total,
                truncated_by_capacity: self.truncated_by_capacity,
                body_preview: self.body_preview,
                body_preview_truncated: self.body_preview_truncated,
            },
            collection: self.collection,
        }
    }
}

struct StartupSyncResult<'a> {
    refresh_session: RefreshSession,
    saved_result: Result<CollectionFetchResult, CollectionQueryError>,
    inbox_result: Result<CollectionFetchResult, CollectionQueryError>,
    recommendation_subtopics: Option<Box<RecommendationSubtopicsState>>,
    reusable_session: Option<ReusableBackendSession<'a>>,
    tls_session_cache: Option<SerializedClientSession>,
}

struct ReusableBackendSession<'a> {
    session: BackendTlsSession<'a>,
    network_address: embassy_net::Ipv4Cidr,
    last_used_ms: u64,
}

impl ReusableBackendSession<'_> {
    fn is_usable_on(&self, stack: Stack<'static>, now_ms: u64, streaming: bool) -> bool {
        stack.is_link_up()
            && stack
                .config_v4()
                .is_some_and(|config| config.address == self.network_address)
            && is_reusable_session_age_usable(self.last_used_ms, now_ms, streaming)
    }

    fn mark_used(&mut self, now_ms: u64) {
        self.last_used_ms = now_ms;
    }
}

struct ConnectedBackendSession<'a> {
    session: BackendTlsSession<'a>,
    network_address: embassy_net::Ipv4Cidr,
    metrics: RequestMetrics,
}

#[derive(Debug, Clone, Copy, Eq, PartialEq)]
enum RequestClass {
    AuthRefresh,
    BufferedMetadata,
    StreamingPackage,
}

impl RequestClass {
    const fn label(self) -> &'static str {
        match self {
            Self::AuthRefresh => "auth_refresh",
            Self::BufferedMetadata => "buffered_metadata",
            Self::StreamingPackage => "streaming_package",
        }
    }

    const fn is_streaming(self) -> bool {
        matches!(self, Self::StreamingPackage)
    }

    const fn connect_timeout_secs(self) -> u64 {
        let _ = self;
        CONNECT_TIMEOUT_SECS
    }

    const fn tls_handshake_timeout_secs(self) -> u64 {
        match self {
            Self::AuthRefresh => AUTH_REFRESH_TLS_HANDSHAKE_TIMEOUT_SECS,
            Self::BufferedMetadata => BUFFERED_METADATA_TLS_HANDSHAKE_TIMEOUT_SECS,
            Self::StreamingPackage => STREAMING_PACKAGE_TLS_HANDSHAKE_TIMEOUT_SECS,
        }
    }

    const fn io_timeout_secs(self) -> u64 {
        match self {
            Self::AuthRefresh => AUTH_REFRESH_IO_TIMEOUT_SECS,
            Self::BufferedMetadata => BUFFERED_METADATA_IO_TIMEOUT_SECS,
            Self::StreamingPackage => STREAMING_PACKAGE_IO_TIMEOUT_SECS,
        }
    }

    const fn socket_timeout_secs(self) -> u64 {
        self.io_timeout_secs()
    }

    const fn network_ready_timeout_secs(self) -> u64 {
        match self {
            Self::AuthRefresh => AUTH_REFRESH_NETWORK_READY_TIMEOUT_SECS,
            Self::BufferedMetadata => BUFFERED_METADATA_NETWORK_READY_TIMEOUT_SECS,
            Self::StreamingPackage => STREAMING_PACKAGE_NETWORK_READY_TIMEOUT_SECS,
        }
    }

    fn network_ready_max_timeout_secs(self, reason: &str) -> u64 {
        if matches!(self, Self::StreamingPackage) && reason == "package_retry" {
            PACKAGE_RETRY_NETWORK_READY_MAX_TIMEOUT_SECS
        } else {
            self.network_ready_timeout_secs()
        }
    }
}

#[derive(Debug, Clone, Copy, Eq, PartialEq)]
enum BackendEndpointSource {
    Dns,
    Cached,
}

#[derive(Debug, Clone, Copy, Eq, PartialEq)]
struct ResolvedBackendRemote {
    addr: Ipv4Addr,
    source: BackendEndpointSource,
    cache_age_ms: Option<u32>,
    session_epoch: Option<u32>,
}

#[derive(Clone, Copy)]
struct BackendRequestContext<'a> {
    stack: Stack<'static>,
    tls: TlsReference<'a>,
    ca_chain: &'a Certificate<'static>,
    tcp_client: &'a BackendTcpClient<'a>,
    tcp_state: &'a BackendTcpClientState,
}

#[derive(Debug, Clone, Copy, Eq, PartialEq)]
enum BackendCommand {
    PrepareContent(PrepareContentRequest),
    LoadCollection(CollectionEndpoint),
    LoadReaderPauseDetail(ReaderPauseDetailRequest),
    ToggleReaderSaved(ReaderSavedToggleRequest),
    ToggleReaderSubscription(ReaderSubscriptionToggleRequest),
    LoadRecommendationSubtopics,
    LoadRecommendationTopic(RecommendationTopicRequest),
}

#[derive(Debug, Clone, Copy, Eq, PartialEq)]
struct HttpResponse<'a> {
    status: u16,
    body: &'a str,
    connection_reusable: bool,
}

#[derive(Debug, Clone, Copy, Eq, PartialEq)]
struct HttpRequest<'a> {
    trace: TraceContext,
    class: RequestClass,
    method: &'a str,
    path: &'a str,
    content_type: Option<&'a str>,
    bearer_token: Option<&'a str>,
    body: &'a [u8],
    connection_close: bool,
}

#[derive(Debug, Clone, Copy, Eq, PartialEq)]
struct HttpResponseMetadata {
    status: u16,
    body_start: usize,
    content_length: Option<usize>,
    chunked: bool,
    connection_close: bool,
}

#[derive(Debug, Clone, Copy, Eq, PartialEq)]
struct StreamingHttpResponse {
    status: u16,
    connection_reusable: bool,
    prepare_progress: Option<PrepareProgressState>,
}

#[derive(Debug, Clone, Copy, Eq, PartialEq)]
struct PrepareProgressState {
    download_steps: u16,
    total_steps: u16,
}

#[derive(Debug, Clone, Copy)]
struct PrepareProgressReporter {
    content_id: InlineText<{ domain::content::CONTENT_ID_MAX_BYTES }>,
    download_steps: u16,
    total_steps: u16,
    last_progress: PrepareContentProgress,
}

impl PrepareProgressReporter {
    fn new(content_id: InlineText<{ domain::content::CONTENT_ID_MAX_BYTES }>) -> Self {
        Self {
            content_id,
            download_steps: PREPARE_PROGRESS_MIN_DOWNLOAD_STEPS,
            total_steps: PREPARE_PROGRESS_MIN_DOWNLOAD_STEPS + PREPARE_PROGRESS_FIXED_STEPS,
            last_progress: PrepareContentProgress::connecting(),
        }
    }

    fn begin_download(&mut self, total_bytes: Option<usize>) {
        if let Some(total_bytes) = total_bytes {
            self.download_steps = prepare_download_step_count(total_bytes);
            self.total_steps = self.download_steps + PREPARE_PROGRESS_FIXED_STEPS;
        }

        self.publish(PrepareContentProgress {
            phase: PrepareContentPhase::Downloading,
            completed_steps: 1,
            total_steps: self.total_steps,
        });
    }

    fn publish_download_progress(&mut self, received_bytes: usize, total_bytes: Option<usize>) {
        let completed_download_steps = match total_bytes {
            Some(total_bytes) if total_bytes > 0 => {
                let scaled = ((received_bytes as u64 * self.download_steps as u64)
                    / total_bytes as u64) as u16;
                if received_bytes > 0 { scaled.max(1) } else { 0 }
            }
            _ => ((received_bytes / PREPARE_PROGRESS_DOWNLOAD_STEP_BYTES) as u16)
                .min(self.download_steps)
                .max(u16::from(received_bytes > 0)),
        };

        self.publish(PrepareContentProgress {
            phase: PrepareContentPhase::Downloading,
            completed_steps: 1 + completed_download_steps.min(self.download_steps),
            total_steps: self.total_steps,
        });
    }

    fn publish(&mut self, progress: PrepareContentProgress) {
        if progress == self.last_progress {
            return;
        }

        self.last_progress = progress;
        publish_event(
            Event::ContentPrepareProgress {
                content_id: self.content_id,
                progress,
            },
            now_ms(),
        );
    }

    const fn state(&self) -> PrepareProgressState {
        PrepareProgressState {
            download_steps: self.download_steps,
            total_steps: self.total_steps,
        }
    }
}

#[derive(Debug, Clone, Copy, Eq, PartialEq)]
struct RequestMetrics {
    trace: TraceContext,
    class: RequestClass,
    started_ms: u64,
    dns_ms: u64,
    connect_ms: u64,
    tls_ms: u64,
    first_byte_ms: Option<u64>,
    total_ms: u64,
    reused_session: bool,
    tls_resume_offered: bool,
    streaming: bool,
    header_bytes: usize,
    body_bytes: usize,
    response_bytes: usize,
    response_buffer_capacity: usize,
    response_buffer_headroom: usize,
    content_length: usize,
    content_length_known: bool,
    stream_header_capacity: usize,
    stream_header_headroom: usize,
}

impl RequestMetrics {
    fn new(trace: TraceContext, reused_session: bool, class: RequestClass) -> Self {
        Self {
            trace,
            class,
            started_ms: now_ms(),
            dns_ms: 0,
            connect_ms: 0,
            tls_ms: 0,
            first_byte_ms: None,
            total_ms: 0,
            reused_session,
            tls_resume_offered: false,
            streaming: class.is_streaming(),
            header_bytes: 0,
            body_bytes: 0,
            response_bytes: 0,
            response_buffer_capacity: 0,
            response_buffer_headroom: 0,
            content_length: 0,
            content_length_known: false,
            stream_header_capacity: 0,
            stream_header_headroom: 0,
        }
    }

    fn elapsed_ms(&self) -> u64 {
        now_ms().saturating_sub(self.started_ms)
    }

    fn mark_first_byte(&mut self) {
        if self.first_byte_ms.is_none() {
            self.first_byte_ms = Some(self.elapsed_ms());
        }
    }

    fn finish(&mut self) {
        self.total_ms = self.elapsed_ms();
    }
}

fn next_request_trace(sync_id: u32) -> TraceContext {
    TraceContext {
        sync_id,
        req_id: next_request_id(),
    }
}

pub(crate) fn log_static_inventory() {
    crate::memtrace!(
        "static_inventory",
        "component" = "backend",
        "at_ms" = now_ms(),
        "driver_loop_future_storage" = "external_pinned_box",
        "backend_tcp_state_bytes" = size_of::<BackendTcpClientState>(),
        "http_request_bytes" = size_of::<HttpRequest<'static>>(),
        "http_response_metadata_bytes" = size_of::<HttpResponseMetadata>(),
        "request_metrics_bytes" = size_of::<RequestMetrics>(),
        "reusable_session_bytes" = size_of::<ReusableBackendSession<'static>>(),
        "active_access_session_bytes" = size_of::<ActiveAccessSession>(),
        "collection_fetch_summary_bytes" = size_of::<CollectionFetchSummary>(),
        "http_response_buffer_len" = HTTP_RESPONSE_MAX_LEN,
        "http_response_buffer_storage" = "external_preferred_box",
        "http_stream_header_max_len" = HTTP_STREAM_HEADER_MAX_LEN,
        "http_stream_header_storage" = "external_preferred_box",
        "package_download_chunk_len" = PACKAGE_DOWNLOAD_CHUNK_LEN,
        "package_storage_handoff_chunk_len" = PACKAGE_STORAGE_HANDOFF_CHUNK_LEN,
        "package_download_chunk_source" = transfer_tuning::PACKAGE_TRANSFER_SOURCE,
        "package_download_chunk_storage" = "external_preferred_box",
        "collection_page_limit" = COLLECTION_PAGE_LIMIT,
        "collection_cursor_max_len" = COLLECTION_CURSOR_MAX_LEN,
        "collection_page_path_max_len" = COLLECTION_PAGE_PATH_MAX_LEN,
        "stream_progress_log_interval_bytes" = STREAM_PROGRESS_LOG_INTERVAL_BYTES,
        "tcp_rx_buffer_bytes" = BACKEND_TCP_RX_BUFFER_LEN,
        "tcp_tx_buffer_bytes" = BACKEND_TCP_TX_BUFFER_LEN,
        "auth_refresh_connect_timeout_secs" = RequestClass::AuthRefresh.connect_timeout_secs(),
        "auth_refresh_tls_handshake_timeout_secs" =
            RequestClass::AuthRefresh.tls_handshake_timeout_secs(),
        "auth_refresh_io_timeout_secs" = RequestClass::AuthRefresh.io_timeout_secs(),
        "auth_refresh_network_ready_timeout_secs" =
            RequestClass::AuthRefresh.network_ready_timeout_secs(),
        "buffered_metadata_connect_timeout_secs" =
            RequestClass::BufferedMetadata.connect_timeout_secs(),
        "buffered_metadata_tls_handshake_timeout_secs" =
            RequestClass::BufferedMetadata.tls_handshake_timeout_secs(),
        "buffered_metadata_io_timeout_secs" = RequestClass::BufferedMetadata.io_timeout_secs(),
        "buffered_metadata_network_ready_timeout_secs" =
            RequestClass::BufferedMetadata.network_ready_timeout_secs(),
        "streaming_package_connect_timeout_secs" =
            RequestClass::StreamingPackage.connect_timeout_secs(),
        "streaming_package_tls_handshake_timeout_secs" =
            RequestClass::StreamingPackage.tls_handshake_timeout_secs(),
        "streaming_package_io_timeout_secs" = RequestClass::StreamingPackage.io_timeout_secs(),
        "streaming_package_network_ready_timeout_secs" =
            RequestClass::StreamingPackage.network_ready_timeout_secs(),
        "streaming_package_network_ready_max_timeout_secs" =
            PACKAGE_RETRY_NETWORK_READY_MAX_TIMEOUT_SECS,
        "backend_cmd_queue_capacity" = BACKEND_CMD_QUEUE_CAPACITY,
    );
}

#[derive(Debug, Clone, Copy, Eq, PartialEq)]
enum BackendError {
    Alloc,
    Dns,
    Connect,
    Tls,
    Io,
    InvalidResponse,
    InvalidUtf8,
    ResponseTooLarge,
    MissingField,
}

#[derive(Debug, Clone, Copy, Eq, PartialEq)]
enum RefreshError {
    Rejected(u16),
    Other(BackendError),
}

#[derive(Debug, Clone, Copy, Eq, PartialEq)]
enum IdentityError {
    Rejected(u16),
    Other(BackendError),
}

#[derive(Debug, Clone, Copy, Eq, PartialEq)]
enum CollectionQueryError {
    Rejected(u16),
    Other(BackendError),
}

#[derive(Debug, Clone, Copy, Eq, PartialEq)]
enum PackagePrepareError {
    PendingRemote,
    Rejected(u16),
    Other(BackendError),
}

pub fn initial_pairing_state(
    stored_credential: Option<BackendCredential>,
) -> domain::device::PairingState {
    if select_startup_credential(compile_time_refresh_token(), stored_credential).is_some() {
        domain::device::PairingState::Paired
    } else {
        domain::device::PairingState::Unpaired
    }
}

pub fn install(
    spawner: Spawner,
    stack: Option<Stack<'static>>,
    stored_credential: Option<BackendCredential>,
    rng: RNG<'static>,
    adc1: ADC1<'static>,
) {
    let Some(stack) = stack else {
        info!("backend disabled: internet stack unavailable");
        return;
    };

    let startup = match select_startup_credential(compile_time_refresh_token(), stored_credential) {
        Some(startup) => startup,
        None => {
            info!(
                "backend disabled: no refresh token configured via MOTIF_BACKEND_REFRESH_TOKEN or storage"
            );
            return;
        }
    };

    info!(
        "backend configured: source={} base_url={}",
        startup.source.label(),
        BACKEND_BASE_URL
    );

    if spawner
        .spawn(backend_task(stack, startup, rng, adc1))
        .is_err()
    {
        warn!("backend failed to spawn auth task");
    }
}

pub async fn request_prepare_content(request: PrepareContentRequest) {
    BACKEND_CMD_CH
        .send(BackendCommand::PrepareContent(request))
        .await;
}

pub async fn request_collection_refresh(collection: CollectionKind) {
    let endpoint = match collection {
        CollectionKind::Saved => CollectionEndpoint::Saved,
        CollectionKind::Inbox => CollectionEndpoint::Inbox,
        CollectionKind::Recommendations => CollectionEndpoint::Recommendations,
    };
    BACKEND_CMD_CH
        .send(BackendCommand::LoadCollection(endpoint))
        .await;
}

pub async fn request_reader_pause_detail(request: ReaderPauseDetailRequest) {
    BACKEND_CMD_CH
        .send(BackendCommand::LoadReaderPauseDetail(request))
        .await;
}

pub async fn request_reader_saved_toggle(request: ReaderSavedToggleRequest) {
    BACKEND_CMD_CH
        .send(BackendCommand::ToggleReaderSaved(request))
        .await;
}

pub async fn request_reader_subscription_toggle(request: ReaderSubscriptionToggleRequest) {
    BACKEND_CMD_CH
        .send(BackendCommand::ToggleReaderSubscription(request))
        .await;
}

pub async fn request_recommendation_subtopics() {
    BACKEND_CMD_CH
        .send(BackendCommand::LoadRecommendationSubtopics)
        .await;
}

pub async fn request_recommendation_topic(request: RecommendationTopicRequest) {
    BACKEND_CMD_CH
        .send(BackendCommand::LoadRecommendationTopic(request))
        .await;
}

#[embassy_executor::task]
async fn backend_task(
    stack: Stack<'static>,
    startup: StartupCredential,
    rng: RNG<'static>,
    adc1: ADC1<'static>,
) {
    let _trng_source = TrngSource::new(rng, adc1);
    let mut trng = match Trng::try_new() {
        Ok(trng) => trng,
        Err(_) => {
            log_status(SyncStatus::TransportFailed);
            warn!("backend tls init failed: TRNG unavailable");
            return;
        }
    };

    let mut tls = match Tls::new(&mut trng) {
        Ok(tls) => tls,
        Err(err) => {
            log_status(SyncStatus::TransportFailed);
            warn!("backend tls init failed: {:?}", err);
            return;
        }
    };
    tls.set_debug(MBEDTLS_DEBUG_LEVEL);
    info!(
        "backend tls config debug_level={} in_content_len={} out_content_len={}",
        MBEDTLS_DEBUG_LEVEL,
        mbedtls_rs::sys::MBEDTLS_SSL_IN_CONTENT_LEN,
        mbedtls_rs::sys::MBEDTLS_SSL_OUT_CONTENT_LEN,
    );

    let ca_chain = match backend_ca_chain() {
        Ok(ca_chain) => ca_chain,
        Err(err) => {
            log_status(SyncStatus::TransportFailed);
            warn!("backend ca chain init failed: {:?}", err);
            return;
        }
    };

    let mut current = startup;
    let tcp_state = Box::new(BackendTcpClientState::new());
    let event_loop = crate::memory_policy::try_external_pinned_box(async move {
        loop {
            log_status(SyncStatus::WaitingForNetwork);
            let network = wait_for_network(stack).await;
            info!("backend network ready ip={:?}", network.address);
            log_heap("backend network ready");
            let mut tcp_client = BackendTcpClient::new(stack, tcp_state.as_ref());
            tcp_client.set_timeout(Some(Duration::from_secs(
                RequestClass::StreamingPackage.socket_timeout_secs(),
            )));

            log_status(SyncStatus::RefreshingSession);
            crate::internet::set_probe_suspended(true);
            let startup_sync_id = next_sync_id();
            log_startup_progress(0, STARTUP_SYNC_QUERY_COUNT);
            crate::memtrace!(
                "backend_sync",
                "component" = "backend",
                "at_ms" = now_ms(),
                "action" = "startup_begin",
                "sync_id" = startup_sync_id,
                "req_id" = 0,
            );
            let startup_sync = perform_startup_refresh_and_collection_sync(
                stack,
                tls.reference(),
                &ca_chain,
                &tcp_client,
                &current.credential,
                startup_sync_id,
            )
            .await;
            crate::internet::set_probe_suspended(false);

            let startup_sync = match startup_sync {
                Ok(result) => result,
                Err(RefreshError::Rejected(status)) => {
                    crate::memtrace!(
                        "backend_sync",
                        "component" = "backend",
                        "at_ms" = now_ms(),
                        "action" = "startup_auth_failed",
                        "sync_id" = startup_sync_id,
                        "req_id" = 0,
                        "status" = status,
                    );
                    log_status(SyncStatus::AuthFailed);
                    info!(
                        "backend refresh rejected status={} source={}",
                        status,
                        current.source.label(),
                    );
                    return;
                }
                Err(RefreshError::Other(err)) => {
                    crate::memtrace!(
                        "backend_sync",
                        "component" = "backend",
                        "at_ms" = now_ms(),
                        "action" = "startup_transport_failed",
                        "sync_id" = startup_sync_id,
                        "req_id" = 0,
                        "error" = backend_error_label(err),
                    );
                    log_status(SyncStatus::TransportFailed);
                    warn!("backend refresh failed: {:?}", err);
                    Timer::after(Duration::from_millis(RETRY_BACKOFF_MS)).await;
                    continue;
                }
            };
            crate::memtrace!(
                "backend_sync",
                "component" = "backend",
                "at_ms" = now_ms(),
                "action" = "startup_ok",
                "sync_id" = startup_sync_id,
                "req_id" = 0,
                "expires_in" = startup_sync.refresh_session.expires_in,
            );

            info!(
                "backend refresh ok expires_in={}s",
                startup_sync.refresh_session.expires_in
            );

            match BackendCredential::from_refresh_token(
                startup_sync.refresh_session.refresh_token.as_str(),
            ) {
                Ok(credential) => {
                    current = StartupCredential {
                        credential,
                        source: CredentialSource::Stored,
                    };
                    persist_backend_credential(credential).await;
                    info!("backend credential persisted");
                }
                Err(err) => {
                    info!("backend credential persistence skipped: {:?}", err);
                }
            }
            let mut access_session = Some(ActiveAccessSession::from_refresh_session(
                &startup_sync.refresh_session,
                now_ms(),
            ));
            let initial_reusable_session = startup_sync.reusable_session;
            let initial_tls_session_cache = startup_sync.tls_session_cache;

            sync_one_collection(
                CollectionKind::Saved,
                startup_sync.saved_result,
                "backend saved",
            )
            .await;
            sync_one_collection(
                CollectionKind::Inbox,
                startup_sync.inbox_result,
                "backend inbox",
            )
            .await;
            if let Some(subtopics) = startup_sync.recommendation_subtopics {
                persist_and_publish_recommendation_subtopics(
                    TraceContext {
                        sync_id: startup_sync_id,
                        req_id: 0,
                    },
                    *subtopics,
                    "backend recommendation subtopics",
                )
                .await;
            }
            log_status(SyncStatus::Ready);
            log_heap("backend ready");
            run_backend_command_loop(
                stack,
                tls.reference(),
                &ca_chain,
                &tcp_client,
                tcp_state.as_ref(),
                &mut current,
                &mut access_session,
                initial_reusable_session,
                initial_tls_session_cache,
            )
            .await;
        }
    });
    let event_loop = match event_loop {
        Ok(event_loop) => event_loop,
        Err(_) => {
            log_status(SyncStatus::TransportFailed);
            warn!("backend event loop alloc failed");
            return;
        }
    };
    event_loop.await;
}

#[allow(clippy::too_many_arguments)]
async fn run_backend_command_loop<'a>(
    stack: Stack<'static>,
    tls: TlsReference<'a>,
    ca_chain: &'a Certificate<'static>,
    tcp_client: &'a BackendTcpClient<'a>,
    tcp_state: &'a BackendTcpClientState,
    current: &mut StartupCredential,
    access_session: &mut Option<ActiveAccessSession>,
    initial_reusable_session: Option<ReusableBackendSession<'a>>,
    initial_tls_session_cache: Option<SerializedClientSession>,
) {
    let mut reusable_session: Option<ReusableBackendSession<'a>> = initial_reusable_session;
    let mut tls_session_cache = initial_tls_session_cache;
    let context = BackendRequestContext {
        stack,
        tls,
        ca_chain,
        tcp_client,
        tcp_state,
    };

    loop {
        let command = if reusable_session.is_some() {
            match select(
                BACKEND_CMD_CH.receive(),
                Timer::after(Duration::from_millis(
                    reusable_session_idle_reap_timeout_ms(),
                )),
            )
            .await
            {
                Either::First(command) => Some(command),
                Either::Second(()) => {
                    let idle_age_ms = reusable_session
                        .as_ref()
                        .map(|session| now_ms().saturating_sub(session.last_used_ms))
                        .unwrap_or_default();
                    info!(
                        "backend reusable session idle reap age_ms={} idle_limit_ms={}",
                        idle_age_ms,
                        reusable_session_idle_reap_timeout_ms(),
                    );
                    close_reusable_session(&mut reusable_session, "idle reap").await;
                    None
                }
            }
        } else {
            Some(BACKEND_CMD_CH.receive().await)
        };

        let Some(command) = command else {
            continue;
        };

        match command {
            BackendCommand::PrepareContent(request) => {
                handle_prepare_content_request(
                    context,
                    current,
                    access_session,
                    &mut reusable_session,
                    &mut tls_session_cache,
                    request,
                )
                .await;
                log_status(SyncStatus::Ready);
            }
            BackendCommand::LoadCollection(endpoint) => {
                handle_collection_refresh_request(
                    context,
                    current,
                    access_session,
                    &mut reusable_session,
                    &mut tls_session_cache,
                    endpoint,
                )
                .await;
                log_status(SyncStatus::Ready);
            }
            BackendCommand::LoadReaderPauseDetail(request) => {
                handle_reader_pause_detail_request(
                    context,
                    current,
                    access_session,
                    &mut reusable_session,
                    &mut tls_session_cache,
                    request,
                )
                .await;
                log_status(SyncStatus::Ready);
            }
            BackendCommand::ToggleReaderSaved(request) => {
                handle_reader_saved_toggle_request(
                    context,
                    current,
                    access_session,
                    &mut reusable_session,
                    &mut tls_session_cache,
                    request,
                )
                .await;
                log_status(SyncStatus::Ready);
            }
            BackendCommand::ToggleReaderSubscription(request) => {
                handle_reader_subscription_toggle_request(
                    context,
                    current,
                    access_session,
                    &mut reusable_session,
                    &mut tls_session_cache,
                    request,
                )
                .await;
                log_status(SyncStatus::Ready);
            }
            BackendCommand::LoadRecommendationSubtopics => {
                handle_recommendation_subtopics_request(
                    context,
                    current,
                    access_session,
                    &mut reusable_session,
                    &mut tls_session_cache,
                )
                .await;
                log_status(SyncStatus::Ready);
            }
            BackendCommand::LoadRecommendationTopic(request) => {
                handle_recommendation_topic_request(
                    context,
                    current,
                    access_session,
                    &mut reusable_session,
                    &mut tls_session_cache,
                    request,
                )
                .await;
                log_status(SyncStatus::Ready);
            }
        }
    }
}

async fn wait_for_network(stack: Stack<'static>) -> NetworkReady {
    loop {
        if stack.is_link_up()
            && crate::internet::backend_path_ready()
            && let Some(config) = stack.config_v4()
        {
            return NetworkReady {
                address: config.address,
            };
        }

        Timer::after(Duration::from_millis(NETWORK_POLL_MS)).await;
    }
}

async fn perform_health_check(
    stack: Stack<'static>,
    tls: TlsReference<'_>,
    ca_chain: &Certificate<'static>,
    tcp_state: &BackendTcpClientState,
) -> Result<(), BackendError> {
    let mut response_buffer = allocate_standard_response_buffer(HEALTH_PATH)?;
    let mut tls_session_cache = None;
    let mut last_error = None;
    let mut attempt = 0;
    while attempt < 3 {
        let response = send_https_request(
            stack,
            tls,
            ca_chain,
            tcp_state,
            &mut tls_session_cache,
            HttpRequest {
                trace: TraceContext::none(),
                class: RequestClass::BufferedMetadata,
                method: "GET",
                path: HEALTH_PATH,
                content_type: None,
                bearer_token: None,
                body: b"",
                connection_close: true,
            },
            response_buffer.as_mut_slice(),
        )
        .await;

        match response {
            Ok(response) => {
                if response.status != 200 {
                    info!(
                        "backend health unexpected status={} path={}",
                        response.status, HEALTH_PATH
                    );
                    return Err(BackendError::InvalidResponse);
                }

                return match extract_json_string(response.body, "\"status\"") {
                    Some("ok") => Ok(()),
                    _ => Err(BackendError::MissingField),
                };
            }
            Err(err) => {
                last_error = Some(err);
                attempt += 1;
                if attempt < 3 {
                    warn!("backend health retry attempt={} err={:?}", attempt, err);
                    Timer::after(Duration::from_millis(750)).await;
                }
            }
        }
    }

    Err(last_error.unwrap_or(BackendError::Io))
}

async fn perform_refresh(
    stack: Stack<'static>,
    tls: TlsReference<'_>,
    ca_chain: &Certificate<'static>,
    tcp_state: &BackendTcpClientState,
    tls_session_cache: &mut Option<SerializedClientSession>,
    credential: &BackendCredential,
    sync_id: u32,
) -> Result<RefreshSession, RefreshError> {
    let refresh_token = credential
        .refresh_token()
        .map_err(|_| RefreshError::Other(BackendError::InvalidResponse))?;
    info!(
        "backend refresh building request token_len={}",
        refresh_token.len()
    );

    let mut response_buffer =
        allocate_standard_response_buffer(REFRESH_PATH).map_err(RefreshError::Other)?;
    let body = Box::new(
        build_refresh_body(refresh_token)
            .map_err(|_| RefreshError::Other(BackendError::InvalidResponse))?,
    );
    info!("backend refresh request ready body_len={}", body.len());
    let response = send_https_request(
        stack,
        tls,
        ca_chain,
        tcp_state,
        tls_session_cache,
        HttpRequest {
            trace: next_request_trace(sync_id),
            class: RequestClass::AuthRefresh,
            method: "POST",
            path: REFRESH_PATH,
            content_type: Some("application/json"),
            bearer_token: None,
            body: body.as_bytes(),
            connection_close: true,
        },
        response_buffer.as_mut_slice(),
    )
    .await
    .map_err(RefreshError::Other)?;

    if (400..500).contains(&response.status) {
        info!(
            "backend refresh rejected status={} path={}",
            response.status, REFRESH_PATH
        );
        return Err(RefreshError::Rejected(response.status));
    }
    if response.status != 200 {
        info!(
            "backend refresh unexpected status={} path={}",
            response.status, REFRESH_PATH
        );
        return Err(RefreshError::Other(BackendError::InvalidResponse));
    }

    parse_refresh_session(response.body)
}

async fn perform_identity_check(
    stack: Stack<'static>,
    tls: TlsReference<'_>,
    ca_chain: &Certificate<'static>,
    tcp_state: &BackendTcpClientState,
    tls_session_cache: &mut Option<SerializedClientSession>,
    access_token: &str,
    sync_id: u32,
) -> Result<MeProfile, IdentityError> {
    let mut response_buffer =
        allocate_standard_response_buffer(ME_PATH).map_err(IdentityError::Other)?;
    let response = send_https_request(
        stack,
        tls,
        ca_chain,
        tcp_state,
        tls_session_cache,
        HttpRequest {
            trace: next_request_trace(sync_id),
            class: RequestClass::BufferedMetadata,
            method: "GET",
            path: ME_PATH,
            content_type: Some("application/json"),
            bearer_token: Some(access_token),
            body: b"",
            connection_close: true,
        },
        response_buffer.as_mut_slice(),
    )
    .await
    .map_err(IdentityError::Other)?;

    if (400..500).contains(&response.status) {
        info!(
            "backend identity rejected status={} path={}",
            response.status, ME_PATH
        );
        return Err(IdentityError::Rejected(response.status));
    }
    if response.status != 200 {
        info!(
            "backend identity unexpected status={} path={}",
            response.status, ME_PATH
        );
        return Err(IdentityError::Other(BackendError::InvalidResponse));
    }

    parse_me_profile(response.body)
}

async fn sync_collection_manifests(
    stack: Stack<'static>,
    tls: TlsReference<'_>,
    ca_chain: &Certificate<'static>,
    tcp_state: &BackendTcpClientState,
    tls_session_cache: &mut Option<SerializedClientSession>,
    access_token: &str,
) {
    info!("backend startup sync mode=saved+inbox");
    sync_one_collection(
        CollectionKind::Saved,
        perform_saved_content_fetch(
            stack,
            tls,
            ca_chain,
            tcp_state,
            tls_session_cache,
            access_token,
            0,
        )
        .await,
        "backend saved",
    )
    .await;
    sync_one_collection(
        CollectionKind::Inbox,
        perform_inbox_fetch(
            stack,
            tls,
            ca_chain,
            tcp_state,
            tls_session_cache,
            access_token,
            0,
        )
        .await,
        "backend inbox",
    )
    .await;
}

async fn perform_startup_refresh_and_collection_sync<'a>(
    stack: Stack<'static>,
    tls: TlsReference<'a>,
    ca_chain: &Certificate<'static>,
    tcp_client: &'a BackendTcpClient<'a>,
    credential: &BackendCredential,
    sync_id: u32,
) -> Result<StartupSyncResult<'a>, RefreshError> {
    let mut attempt = 0usize;
    let mut tls_session_cache = None;

    loop {
        let result = perform_startup_refresh_and_collection_sync_once(
            stack,
            tls,
            ca_chain,
            tcp_client,
            &mut tls_session_cache,
            credential,
            sync_id,
        )
        .await;
        match result {
            Err(RefreshError::Other(err))
                if is_transient_transport_error(err) && attempt + 1 < TRANSPORT_RETRY_ATTEMPTS =>
            {
                attempt += 1;
                warn!("backend startup retry attempt={} err={:?}", attempt, err);
                // Startup sync normally suspends the background probe task to
                // keep the shared socket set focused on refresh + manifest
                // fetches. If the first attempt invalidates backend-path
                // readiness, briefly re-enable probing so the retry waits for a
                // fresh, real connectivity check instead of blindly burning its
                // final attempt on a still-bad path.
                crate::internet::set_probe_suspended(false);
                let recovery = wait_for_backend_request_path_ready(
                    stack,
                    TraceContext { sync_id, req_id: 0 },
                    REFRESH_PATH,
                    RequestClass::AuthRefresh,
                    "startup_retry_reprobe",
                )
                .await;
                crate::internet::set_probe_suspended(true);
                recovery.map_err(RefreshError::Other)?;
                Timer::after(Duration::from_millis(TRANSPORT_RETRY_BACKOFF_MS)).await;
            }
            other => return other,
        }
    }
}

async fn perform_startup_refresh_and_collection_sync_once<'a>(
    stack: Stack<'static>,
    tls: TlsReference<'a>,
    ca_chain: &Certificate<'static>,
    tcp_client: &'a BackendTcpClient<'a>,
    tls_session_cache: &mut Option<SerializedClientSession>,
    credential: &BackendCredential,
    sync_id: u32,
) -> Result<StartupSyncResult<'a>, RefreshError> {
    let refresh_token = credential
        .refresh_token()
        .map_err(|_| RefreshError::Other(BackendError::InvalidResponse))?;
    info!(
        "backend refresh building request token_len={}",
        refresh_token.len()
    );

    let refresh_trace = next_request_trace(sync_id);
    let mut refresh_metrics = RequestMetrics::new(refresh_trace, false, RequestClass::AuthRefresh);
    log_request_phase(
        refresh_trace,
        REFRESH_PATH,
        RequestClass::AuthRefresh,
        "open",
        0,
    );
    let resolved_remote = resolve_backend_remote(
        stack,
        refresh_trace,
        REFRESH_PATH,
        RequestClass::AuthRefresh,
        &mut refresh_metrics,
    )
    .await
    .map_err(RefreshError::Other)?;
    let connect_started_ms = now_ms();
    log_request_phase(
        refresh_trace,
        REFRESH_PATH,
        RequestClass::AuthRefresh,
        "dns_ok",
        refresh_metrics.dns_ms,
    );
    let connection = with_timeout(
        Duration::from_secs(RequestClass::AuthRefresh.connect_timeout_secs()),
        tcp_client.connect(SocketAddr::new(
            IpAddr::V4(resolved_remote.addr),
            BACKEND_PORT,
        )),
    )
    .await
    .map_err(|_| {
        crate::internet::invalidate_backend_path("connect_timeout");
        warn!("backend request connect timed out path={}", REFRESH_PATH);
        log_request_heap(REFRESH_PATH, "connect timeout");
        RefreshError::Other(BackendError::Connect)
    })?
    .map_err(|_| {
        crate::internet::invalidate_backend_path("connect_failed");
        warn!("backend request connect failed path={}", REFRESH_PATH);
        log_request_heap(REFRESH_PATH, "connect failed");
        RefreshError::Other(BackendError::Connect)
    })?;
    crate::internet::record_backend_endpoint(resolved_remote.addr, "request_connect_ok");
    refresh_metrics.connect_ms = elapsed_since_ms(connect_started_ms);
    if matches!(resolved_remote.source, BackendEndpointSource::Cached) {
        info!(
            "backend request dns fallback succeeded path={} remote_ip={} cache_age_ms={} session_epoch={} connect_ms={}",
            REFRESH_PATH,
            resolved_remote.addr,
            resolved_remote.cache_age_ms.unwrap_or_default(),
            resolved_remote.session_epoch.unwrap_or_default(),
            refresh_metrics.connect_ms
        );
    }
    log_request_phase(
        refresh_trace,
        REFRESH_PATH,
        RequestClass::AuthRefresh,
        "connect_ok",
        refresh_metrics.elapsed_ms(),
    );
    log_request_heap(REFRESH_PATH, "tls setup start");
    log_request_phase(
        refresh_trace,
        REFRESH_PATH,
        RequestClass::AuthRefresh,
        "tls_setup_start",
        refresh_metrics.elapsed_ms(),
    );
    let mut session = open_tls_session(tls, ca_chain, CompatConnection::new(connection))
        .inspect_err(|_err| {
            warn!("backend request tls setup failed path={}", REFRESH_PATH);
            log_request_heap(REFRESH_PATH, "tls setup failed");
        })
        .map_err(RefreshError::Other)?;
    prepare_tls_session_resume(
        &mut session,
        tls_session_cache,
        REFRESH_PATH,
        false,
        &mut refresh_metrics,
    );
    log_request_heap(REFRESH_PATH, "tls setup ok");
    log_request_phase(
        refresh_trace,
        REFRESH_PATH,
        RequestClass::AuthRefresh,
        "tls_setup_ok",
        refresh_metrics.elapsed_ms(),
    );
    let tls_started_ms = now_ms();
    log_request_heap(REFRESH_PATH, "tls handshake start");
    log_request_phase(
        refresh_trace,
        REFRESH_PATH,
        RequestClass::AuthRefresh,
        "tls_handshake_start",
        refresh_metrics.elapsed_ms(),
    );
    if let Err(err) =
        await_tls_handshake(&mut session, REFRESH_PATH, RequestClass::AuthRefresh).await
    {
        discard_failed_tls_session_resume(tls_session_cache, REFRESH_PATH, false, &refresh_metrics);
        crate::internet::invalidate_backend_path(backend_error_label(err));
        return Err(RefreshError::Other(err));
    }
    refresh_metrics.tls_ms = elapsed_since_ms(tls_started_ms);
    log_request_heap(REFRESH_PATH, "tls handshake ok");
    log_request_phase(
        refresh_trace,
        REFRESH_PATH,
        RequestClass::AuthRefresh,
        "tls_handshake_ok",
        refresh_metrics.elapsed_ms(),
    );
    let verification_flags = session.tls_verification_details();
    if verification_flags != 0 {
        info!(
            "backend request tls verification flags path={} flags=0x{:08x}",
            REFRESH_PATH, verification_flags
        );
    }
    cache_negotiated_tls_session(&session, tls_session_cache, REFRESH_PATH, false);

    let mut response_buffer =
        allocate_standard_response_buffer(REFRESH_PATH).map_err(RefreshError::Other)?;
    let body = Box::new(
        build_refresh_body(refresh_token)
            .map_err(|_| RefreshError::Other(BackendError::InvalidResponse))?,
    );
    info!("backend refresh request ready body_len={}", body.len());
    let refresh_response = send_https_request_over_session_with_metrics(
        &mut session,
        HttpRequest {
            trace: refresh_trace,
            class: RequestClass::AuthRefresh,
            method: "POST",
            path: REFRESH_PATH,
            content_type: Some("application/json"),
            bearer_token: None,
            body: body.as_bytes(),
            connection_close: false,
        },
        response_buffer.as_mut_slice(),
        refresh_metrics,
    )
    .await
    .map_err(RefreshError::Other)?;

    if (400..500).contains(&refresh_response.status) {
        info!(
            "backend refresh rejected status={} path={}",
            refresh_response.status, REFRESH_PATH
        );
        if let Err(err) = session.close().await {
            info!("backend tls close failed: {:?}", err);
        }
        return Err(RefreshError::Rejected(refresh_response.status));
    }
    if refresh_response.status != 200 {
        info!(
            "backend refresh unexpected status={} path={}",
            refresh_response.status, REFRESH_PATH
        );
        if let Err(err) = session.close().await {
            info!("backend tls close failed: {:?}", err);
        }
        return Err(RefreshError::Other(BackendError::InvalidResponse));
    }

    let refresh_session = parse_refresh_session(refresh_response.body)?;
    log_startup_progress(1, STARTUP_SYNC_QUERY_COUNT);
    log_status(SyncStatus::SyncingContent);
    info!("backend startup sync mode=saved+inbox+recommendation_subtopics");

    let mut saved_result = perform_saved_content_fetch_over_session(
        &mut session,
        refresh_session.access_token.as_str(),
        false,
        sync_id,
    )
    .await;
    log_startup_progress(2, STARTUP_SYNC_QUERY_COUNT);

    if let Some(err) = startup_collection_fetch_transport_error(&saved_result) {
        if let Err(close_err) = session.close().await {
            info!("backend tls close failed: {:?}", close_err);
        }
        return Err(RefreshError::Other(err));
    }

    let inbox_result = perform_inbox_fetch_over_session(
        &mut session,
        refresh_session.access_token.as_str(),
        false,
        sync_id,
    )
    .await;
    log_startup_progress(3, STARTUP_SYNC_QUERY_COUNT);

    if let Some(err) = startup_collection_fetch_transport_error(&inbox_result) {
        if let Err(close_err) = session.close().await {
            info!("backend tls close failed: {:?}", close_err);
        }
        return Err(RefreshError::Other(err));
    }

    if let Ok(result) = &mut saved_result
        && inbox_result.is_ok()
    {
        prefetch_startup_saved_content(
            &mut session,
            refresh_session.access_token.as_str(),
            result,
            sync_id,
        )
        .await;
    }

    let mut recommendation_subtopics = None;
    let mut reusable_session_failed = false;
    if saved_result.is_ok() && inbox_result.is_ok() {
        match perform_recommendation_subtopics_fetch_over_session(
            &mut session,
            refresh_session.access_token.as_str(),
            false,
            sync_id,
        )
        .await
        {
            Ok(subtopics) => {
                recommendation_subtopics = Some(Box::new(subtopics));
            }
            Err(CollectionQueryError::Rejected(status)) => {
                info!(
                    "backend startup recommendation subtopics rejected status={}",
                    status
                );
            }
            Err(CollectionQueryError::Other(err)) => {
                info!(
                    "backend startup recommendation subtopics failed err={:?}",
                    err
                );
                if is_transient_transport_error(err) {
                    reusable_session_failed = true;
                }
            }
        }
        log_startup_progress(4, STARTUP_SYNC_QUERY_COUNT);
    }

    let reusable_session = if saved_result.is_ok()
        && inbox_result.is_ok()
        && !reusable_session_failed
    {
        if let Some(network_address) = current_network_address(stack) {
            info!(
                "backend startup session retained for steady state network_ip={:?}",
                network_address
            );
            Some(ReusableBackendSession {
                session,
                network_address,
                last_used_ms: now_ms(),
            })
        } else {
            info!("backend startup session closing before steady state reason=missing_network");
            if let Err(err) = session.close().await {
                info!("backend tls close failed reason=startup done err={:?}", err);
            }
            None
        }
    } else if reusable_session_failed {
        warn!(
            "backend startup session closing before steady state reason=recommendation_subtopics_failed"
        );
        if let Err(err) = session.close().await {
            info!("backend tls close failed reason=startup done err={:?}", err);
        }
        None
    } else {
        warn!("backend startup session closing before steady state reason=sync_failed");
        if let Err(err) = session.close().await {
            info!("backend tls close failed reason=startup done err={:?}", err);
        }
        None
    };

    Ok(StartupSyncResult {
        refresh_session,
        saved_result,
        inbox_result,
        recommendation_subtopics,
        reusable_session,
        tls_session_cache: tls_session_cache.clone(),
    })
}

async fn prefetch_startup_saved_content<T>(
    session: &mut Session<'_, T>,
    access_token: &str,
    result: &mut CollectionFetchResult,
    sync_id: u32,
) where
    T: AsyncRead07 + AsyncWrite07,
{
    if !STARTUP_SAVED_PREFETCH_ENABLED {
        return;
    }

    let mut prefetched = 0usize;
    let mut index = 0usize;
    while index < result.collection.len() && prefetched < STARTUP_SAVED_PREFETCH_LIMIT {
        let item = result.collection.items[index];
        index += 1;

        if !item.can_prepare() {
            continue;
        }
        let request = PrepareContentRequest::from_manifest(CollectionKind::Saved, item);
        match fetch_and_stage_package_over_session(session, access_token, request, sync_id).await {
            Ok(_snapshot) => {
                mark_prefetched_item_cached(&mut result.collection, &request);
                prefetched += 1;
                info!(
                    "backend startup saved prefetch ok content_id={} count={}",
                    request.content_id.as_str(),
                    prefetched,
                );
            }
            Err(PackagePrepareError::PendingRemote) => {
                info!(
                    "backend startup saved prefetch pending remote content_id={}",
                    request.content_id.as_str(),
                );
            }
            Err(PackagePrepareError::Rejected(status)) => {
                info!(
                    "backend startup saved prefetch rejected status={} content_id={}",
                    status,
                    request.content_id.as_str(),
                );
                break;
            }
            Err(PackagePrepareError::Other(err)) => {
                info!(
                    "backend startup saved prefetch failed content_id={} err={:?}",
                    request.content_id.as_str(),
                    err,
                );
                break;
            }
        }
    }
}

fn mark_prefetched_item_cached(
    collection: &mut CollectionManifestState,
    request: &PrepareContentRequest,
) {
    let _ = collection.update_package_state(&request.remote_item_id, PackageState::Cached);
}

#[allow(clippy::too_many_arguments)]
async fn ensure_access_session<'a>(
    stack: Stack<'static>,
    tls: TlsReference<'a>,
    ca_chain: &Certificate<'static>,
    tcp_state: &'a BackendTcpClientState,
    current: &mut StartupCredential,
    access_session: &mut Option<ActiveAccessSession>,
    reusable_session: &mut Option<ReusableBackendSession<'a>>,
    tls_session_cache: &mut Option<SerializedClientSession>,
    sync_id: u32,
) -> Result<(), RefreshError> {
    let now_ms = now_ms();
    match access_session.as_ref() {
        Some(session) if session.is_valid_at(now_ms) => {
            info!(
                "backend access session reuse valid_for_ms={} token_len={}",
                session.valid_until_ms.saturating_sub(now_ms),
                session.access_token.len(),
            );
            return Ok(());
        }
        Some(session) => {
            info!(
                "backend access session refresh reason=expired expired_by_ms={} token_len={}",
                now_ms.saturating_sub(session.valid_until_ms),
                session.access_token.len(),
            );
        }
        None => {
            info!("backend access session refresh reason=missing");
        }
    }

    close_reusable_session(reusable_session, "refresh").await;
    log_status(SyncStatus::RefreshingSession);
    let mut refresh_attempt = 0usize;
    let refresh_session = loop {
        wait_for_backend_request_path_ready(
            stack,
            TraceContext { sync_id, req_id: 0 },
            REFRESH_PATH,
            RequestClass::AuthRefresh,
            if refresh_attempt == 0 {
                "prepare_refresh"
            } else {
                "prepare_refresh_retry"
            },
        )
        .await
        .map_err(RefreshError::Other)?;

        match perform_refresh(
            stack,
            tls,
            ca_chain,
            tcp_state,
            tls_session_cache,
            &current.credential,
            sync_id,
        )
        .await
        {
            Err(RefreshError::Other(err))
                if is_transient_transport_error(err)
                    && refresh_attempt + 1 < TRANSPORT_RETRY_ATTEMPTS =>
            {
                refresh_attempt += 1;
                info!(
                    "backend access session refresh retry attempt={} err={:?}",
                    refresh_attempt, err
                );
                Timer::after(Duration::from_millis(TRANSPORT_RETRY_BACKOFF_MS)).await;
            }
            other => break other?,
        }
    };
    info!(
        "backend access session refreshed expires_in={}s",
        refresh_session.expires_in
    );

    if let Ok(credential) =
        BackendCredential::from_refresh_token(refresh_session.refresh_token.as_str())
    {
        *current = StartupCredential {
            credential,
            source: CredentialSource::Stored,
        };
        persist_backend_credential(credential).await;
        info!("backend credential persisted");
    }

    *access_session = Some(ActiveAccessSession::from_refresh_session(
        &refresh_session,
        now_ms,
    ));
    Ok(())
}

async fn sync_one_collection(
    kind: CollectionKind,
    result: Result<CollectionFetchResult, CollectionQueryError>,
    label: &str,
) {
    match result {
        Ok(result) => {
            let CollectionFetchResult {
                summary,
                collection,
            } = result;
            let collection = match content_storage::persist_snapshot_traced(
                summary.trace,
                kind,
                *collection.as_ref(),
            )
            .await
            {
                Ok(snapshot) => snapshot,
                Err(err) => {
                    info!("{} persist failed: {:?}", label, err);
                    *collection
                }
            };
            publish_event(
                Event::CollectionContentUpdated(kind, Box::new(collection)),
                now_ms(),
            );
            info!(
                "{} ok item_count={} pages={} body_bytes_total={} truncated={} next_cursor={}",
                label,
                summary.item_count,
                summary.page_count,
                summary.body_bytes_total,
                summary.truncated_by_capacity,
                if summary.next_cursor_present {
                    "present"
                } else {
                    "null"
                }
            );
            if let Some(preview) = summary.body_preview {
                if summary.body_preview_truncated {
                    info!("{} preview={}...", label, preview);
                } else {
                    info!("{} preview={}", label, preview);
                }
            }
        }
        Err(CollectionQueryError::Rejected(status)) => {
            if is_auth_status(status) {
                log_status(SyncStatus::AuthFailed);
            }
            info!("{} rejected status={}", label, status);
        }
        Err(CollectionQueryError::Other(err)) => {
            info!("{} failed: {:?}", label, err);
        }
    }
}

async fn persist_and_publish_recommendation_subtopics(
    trace: TraceContext,
    subtopics: RecommendationSubtopicsState,
    label: &str,
) {
    if let Err(err) =
        content_storage::queue_recommendation_subtopics_write_traced(trace, subtopics).await
    {
        info!(
            "{} persist failed count={} err={:?}",
            label,
            subtopics.len(),
            err,
        );
    }

    publish_event(
        Event::RecommendationSubtopicsUpdated(Box::new(subtopics)),
        now_ms(),
    );
    info!("{} ok count={}", label, subtopics.len());
}

async fn handle_collection_refresh_request<'a>(
    context: BackendRequestContext<'a>,
    current: &mut StartupCredential,
    access_session: &mut Option<ActiveAccessSession>,
    reusable_session: &mut Option<ReusableBackendSession<'a>>,
    tls_session_cache: &mut Option<SerializedClientSession>,
    endpoint: CollectionEndpoint,
) {
    let operation_sync_id = next_sync_id();

    if let Err(err) = ensure_access_session(
        context.stack,
        context.tls,
        context.ca_chain,
        context.tcp_state,
        current,
        access_session,
        reusable_session,
        tls_session_cache,
        operation_sync_id,
    )
    .await
    {
        handle_reader_pause_access_error(err, current, access_session, reusable_session).await;
        return;
    }

    log_status(SyncStatus::SyncingContent);
    let access_token = access_session
        .as_ref()
        .map(|session| session.access_token.clone())
        .unwrap_or_default();
    let result = perform_collection_fetch_paginated_reusing_session(
        context.stack,
        context.tls,
        context.ca_chain,
        context.tcp_client,
        reusable_session,
        tls_session_cache,
        access_token.as_str(),
        operation_sync_id,
        endpoint,
    )
    .await;
    sync_one_collection(
        endpoint.kind(),
        result,
        match endpoint {
            CollectionEndpoint::Inbox => "backend inbox refresh",
            CollectionEndpoint::Saved => "backend saved refresh",
            CollectionEndpoint::Recommendations => "backend recommendation refresh",
        },
    )
    .await;
}

async fn handle_reader_pause_detail_request<'a>(
    context: BackendRequestContext<'a>,
    current: &mut StartupCredential,
    access_session: &mut Option<ActiveAccessSession>,
    reusable_session: &mut Option<ReusableBackendSession<'a>>,
    tls_session_cache: &mut Option<SerializedClientSession>,
    request: ReaderPauseDetailRequest,
) {
    if request.content_id.is_empty() {
        return;
    }

    let operation_sync_id = next_sync_id();
    if let Err(err) = ensure_access_session(
        context.stack,
        context.tls,
        context.ca_chain,
        context.tcp_state,
        current,
        access_session,
        reusable_session,
        tls_session_cache,
        operation_sync_id,
    )
    .await
    {
        handle_reader_pause_access_error(err, current, access_session, reusable_session).await;
        publish_event(
            Event::ReaderPauseDetailFailed {
                content_id: request.content_id,
            },
            now_ms(),
        );
        return;
    }

    log_status(SyncStatus::SyncingContent);
    let access_token = access_session
        .as_ref()
        .map(|session| session.access_token.clone())
        .unwrap_or_default();
    match perform_reader_pause_detail_fetch_reusing_session(
        context.stack,
        context.tls,
        context.ca_chain,
        context.tcp_client,
        reusable_session,
        tls_session_cache,
        request.content_id,
        access_token.as_ref(),
        operation_sync_id,
    )
    .await
    {
        Ok(detail) => {
            publish_event(Event::ReaderPauseDetailLoaded(detail), now_ms());
        }
        Err(CollectionQueryError::Rejected(status)) => {
            if is_auth_status(status) {
                invalidate_access_state(access_session, reusable_session).await;
                log_status(SyncStatus::AuthFailed);
            }
            publish_event(
                Event::ReaderPauseDetailFailed {
                    content_id: request.content_id,
                },
                now_ms(),
            );
        }
        Err(CollectionQueryError::Other(err)) => {
            if is_transient_transport_error(err) {
                *access_session = None;
                log_status(SyncStatus::TransportFailed);
            }
            publish_event(
                Event::ReaderPauseDetailFailed {
                    content_id: request.content_id,
                },
                now_ms(),
            );
        }
    }
}

async fn handle_reader_saved_toggle_request<'a>(
    context: BackendRequestContext<'a>,
    current: &mut StartupCredential,
    access_session: &mut Option<ActiveAccessSession>,
    reusable_session: &mut Option<ReusableBackendSession<'a>>,
    tls_session_cache: &mut Option<SerializedClientSession>,
    request: ReaderSavedToggleRequest,
) {
    if request.content_id.is_empty() {
        return;
    }

    let operation_sync_id = next_sync_id();
    if let Err(err) = ensure_access_session(
        context.stack,
        context.tls,
        context.ca_chain,
        context.tcp_state,
        current,
        access_session,
        reusable_session,
        tls_session_cache,
        operation_sync_id,
    )
    .await
    {
        handle_reader_pause_access_error(err, current, access_session, reusable_session).await;
        publish_event(
            Event::ReaderPauseActionFailed {
                content_id: request.content_id,
                action: domain::reader::ReaderPauseActionKind::Save,
            },
            now_ms(),
        );
        return;
    }

    log_status(SyncStatus::SyncingContent);
    let access_token = access_session
        .as_ref()
        .map(|session| session.access_token.clone())
        .unwrap_or_default();
    let path = match build_reader_save_path(&request.content_id) {
        Ok(path) => path,
        Err(_) => {
            publish_event(
                Event::ReaderPauseActionFailed {
                    content_id: request.content_id,
                    action: domain::reader::ReaderPauseActionKind::Save,
                },
                now_ms(),
            );
            return;
        }
    };
    match perform_reader_pause_mutation_reusing_session(
        context.stack,
        context.tls,
        context.ca_chain,
        context.tcp_client,
        reusable_session,
        tls_session_cache,
        if request.save { "PUT" } else { "DELETE" },
        path.as_str(),
        access_token.as_ref(),
        operation_sync_id,
    )
    .await
    {
        Ok(()) => {
            publish_event(
                Event::ReaderPauseActionApplied {
                    content_id: request.content_id,
                    action: domain::reader::ReaderPauseActionKind::Save,
                    enabled: request.save,
                },
                now_ms(),
            );
            let _ = refresh_reader_pause_detail_after_action(
                context,
                current,
                access_session,
                reusable_session,
                tls_session_cache,
                request.content_id,
                operation_sync_id,
            )
            .await;
            let result = perform_collection_fetch_paginated_reusing_session(
                context.stack,
                context.tls,
                context.ca_chain,
                context.tcp_client,
                reusable_session,
                tls_session_cache,
                access_token.as_ref(),
                operation_sync_id,
                CollectionEndpoint::Saved,
            )
            .await;
            sync_one_collection(CollectionKind::Saved, result, "backend saved refresh").await;
        }
        Err(CollectionQueryError::Rejected(status)) => {
            if is_auth_status(status) {
                invalidate_access_state(access_session, reusable_session).await;
                log_status(SyncStatus::AuthFailed);
            }
            publish_event(
                Event::ReaderPauseActionFailed {
                    content_id: request.content_id,
                    action: domain::reader::ReaderPauseActionKind::Save,
                },
                now_ms(),
            );
        }
        Err(CollectionQueryError::Other(err)) => {
            if is_transient_transport_error(err) {
                *access_session = None;
                log_status(SyncStatus::TransportFailed);
            }
            publish_event(
                Event::ReaderPauseActionFailed {
                    content_id: request.content_id,
                    action: domain::reader::ReaderPauseActionKind::Save,
                },
                now_ms(),
            );
        }
    }
}

async fn handle_reader_subscription_toggle_request<'a>(
    context: BackendRequestContext<'a>,
    current: &mut StartupCredential,
    access_session: &mut Option<ActiveAccessSession>,
    reusable_session: &mut Option<ReusableBackendSession<'a>>,
    tls_session_cache: &mut Option<SerializedClientSession>,
    request: ReaderSubscriptionToggleRequest,
) {
    if request.content_id.is_empty() || request.source_id.is_empty() {
        return;
    }

    let operation_sync_id = next_sync_id();
    if let Err(err) = ensure_access_session(
        context.stack,
        context.tls,
        context.ca_chain,
        context.tcp_state,
        current,
        access_session,
        reusable_session,
        tls_session_cache,
        operation_sync_id,
    )
    .await
    {
        handle_reader_pause_access_error(err, current, access_session, reusable_session).await;
        publish_event(
            Event::ReaderPauseActionFailed {
                content_id: request.content_id,
                action: domain::reader::ReaderPauseActionKind::Subscription,
            },
            now_ms(),
        );
        return;
    }

    log_status(SyncStatus::SyncingContent);
    let access_token = access_session
        .as_ref()
        .map(|session| session.access_token.as_str())
        .unwrap_or("");
    let path = match build_reader_source_subscription_path(&request.source_id) {
        Ok(path) => path,
        Err(_) => {
            publish_event(
                Event::ReaderPauseActionFailed {
                    content_id: request.content_id,
                    action: domain::reader::ReaderPauseActionKind::Subscription,
                },
                now_ms(),
            );
            return;
        }
    };
    match perform_reader_pause_mutation_reusing_session(
        context.stack,
        context.tls,
        context.ca_chain,
        context.tcp_client,
        reusable_session,
        tls_session_cache,
        if request.subscribe { "PUT" } else { "DELETE" },
        path.as_str(),
        access_token,
        operation_sync_id,
    )
    .await
    {
        Ok(()) => {
            publish_event(
                Event::ReaderPauseActionApplied {
                    content_id: request.content_id,
                    action: domain::reader::ReaderPauseActionKind::Subscription,
                    enabled: request.subscribe,
                },
                now_ms(),
            );
            let _ = refresh_reader_pause_detail_after_action(
                context,
                current,
                access_session,
                reusable_session,
                tls_session_cache,
                request.content_id,
                operation_sync_id,
            )
            .await;
        }
        Err(CollectionQueryError::Rejected(status)) => {
            if is_auth_status(status) {
                invalidate_access_state(access_session, reusable_session).await;
                log_status(SyncStatus::AuthFailed);
            }
            publish_event(
                Event::ReaderPauseActionFailed {
                    content_id: request.content_id,
                    action: domain::reader::ReaderPauseActionKind::Subscription,
                },
                now_ms(),
            );
        }
        Err(CollectionQueryError::Other(err)) => {
            if is_transient_transport_error(err) {
                *access_session = None;
                log_status(SyncStatus::TransportFailed);
            }
            publish_event(
                Event::ReaderPauseActionFailed {
                    content_id: request.content_id,
                    action: domain::reader::ReaderPauseActionKind::Subscription,
                },
                now_ms(),
            );
        }
    }
}

#[allow(clippy::too_many_arguments)]
async fn refresh_reader_pause_detail_after_action<'a>(
    context: BackendRequestContext<'a>,
    current: &StartupCredential,
    access_session: &mut Option<ActiveAccessSession>,
    reusable_session: &mut Option<ReusableBackendSession<'a>>,
    tls_session_cache: &mut Option<SerializedClientSession>,
    content_id: InlineText<{ domain::content::CONTENT_ID_MAX_BYTES }>,
    sync_id: u32,
) -> Result<(), CollectionQueryError> {
    let access_token = access_session
        .as_ref()
        .map(|session| session.access_token.as_str())
        .unwrap_or("");
    match perform_reader_pause_detail_fetch_reusing_session(
        context.stack,
        context.tls,
        context.ca_chain,
        context.tcp_client,
        reusable_session,
        tls_session_cache,
        content_id,
        access_token,
        sync_id,
    )
    .await
    {
        Ok(detail) => {
            publish_event(Event::ReaderPauseDetailLoaded(detail), now_ms());
            Ok(())
        }
        Err(err) => {
            if matches!(err, CollectionQueryError::Rejected(status) if is_auth_status(status)) {
                warn!(
                    "backend reader pause detail refresh rejected content_id={} source={}",
                    content_id.as_str(),
                    current.source.label(),
                );
            }
            publish_event(Event::ReaderPauseDetailFailed { content_id }, now_ms());
            Err(err)
        }
    }
}

fn startup_collection_fetch_transport_error(
    result: &Result<CollectionFetchResult, CollectionQueryError>,
) -> Option<BackendError> {
    match result {
        Err(CollectionQueryError::Other(err)) if is_transient_transport_error(*err) => Some(*err),
        _ => None,
    }
}

async fn handle_recommendation_subtopics_request<'a>(
    context: BackendRequestContext<'a>,
    current: &mut StartupCredential,
    access_session: &mut Option<ActiveAccessSession>,
    reusable_session: &mut Option<ReusableBackendSession<'a>>,
    tls_session_cache: &mut Option<SerializedClientSession>,
) {
    let operation_sync_id = next_sync_id();

    if let Err(err) = ensure_access_session(
        context.stack,
        context.tls,
        context.ca_chain,
        context.tcp_state,
        current,
        access_session,
        reusable_session,
        tls_session_cache,
        operation_sync_id,
    )
    .await
    {
        handle_recommendation_access_error(err, current, access_session, reusable_session).await;
        publish_event(
            Event::RecommendationSubtopicsUpdated(Box::new(RecommendationSubtopicsState::empty())),
            now_ms(),
        );
        return;
    }

    log_status(SyncStatus::SyncingContent);
    let access_token = access_session
        .as_ref()
        .map(|session| session.access_token.as_str())
        .unwrap_or("");
    match perform_recommendation_subtopics_fetch_reusing_session(
        context.stack,
        context.tls,
        context.ca_chain,
        context.tcp_client,
        reusable_session,
        tls_session_cache,
        access_token,
        operation_sync_id,
    )
    .await
    {
        Ok(subtopics) => {
            persist_and_publish_recommendation_subtopics(
                TraceContext {
                    sync_id: operation_sync_id,
                    req_id: 0,
                },
                subtopics,
                "backend recommendation subtopics",
            )
            .await;
        }
        Err(CollectionQueryError::Rejected(status)) => {
            if is_auth_status(status) {
                invalidate_access_state(access_session, reusable_session).await;
                log_status(SyncStatus::AuthFailed);
            }
            publish_event(
                Event::RecommendationSubtopicsUpdated(Box::new(
                    RecommendationSubtopicsState::empty(),
                )),
                now_ms(),
            );
        }
        Err(CollectionQueryError::Other(err)) => {
            if is_transient_transport_error(err) {
                *access_session = None;
                log_status(SyncStatus::TransportFailed);
            }
            publish_event(
                Event::RecommendationSubtopicsUpdated(Box::new(
                    RecommendationSubtopicsState::empty(),
                )),
                now_ms(),
            );
        }
    }
}

async fn handle_recommendation_topic_request<'a>(
    context: BackendRequestContext<'a>,
    current: &mut StartupCredential,
    access_session: &mut Option<ActiveAccessSession>,
    reusable_session: &mut Option<ReusableBackendSession<'a>>,
    tls_session_cache: &mut Option<SerializedClientSession>,
    request: RecommendationTopicRequest,
) {
    if request.topic_slug.is_empty() {
        publish_event(
            Event::RecommendationTopicContentUpdated {
                topic_slug: request.topic_slug,
                collection: empty_collection_state_box(),
            },
            now_ms(),
        );
        return;
    }

    let operation_sync_id = next_sync_id();
    if let Err(err) = ensure_access_session(
        context.stack,
        context.tls,
        context.ca_chain,
        context.tcp_state,
        current,
        access_session,
        reusable_session,
        tls_session_cache,
        operation_sync_id,
    )
    .await
    {
        handle_recommendation_access_error(err, current, access_session, reusable_session).await;
        publish_event(
            Event::RecommendationTopicContentUpdated {
                topic_slug: request.topic_slug,
                collection: empty_collection_state_box(),
            },
            now_ms(),
        );
        return;
    }

    log_status(SyncStatus::SyncingContent);
    let access_token = access_session
        .as_ref()
        .map(|session| session.access_token.as_str())
        .unwrap_or("");
    let collection = match perform_recommendation_topic_fetch_reusing_session(
        context.stack,
        context.tls,
        context.ca_chain,
        context.tcp_client,
        reusable_session,
        tls_session_cache,
        access_token,
        request.topic_slug,
        operation_sync_id,
    )
    .await
    {
        Ok(result) => result.collection,
        Err(CollectionQueryError::Rejected(status)) => {
            if is_auth_status(status) {
                invalidate_access_state(access_session, reusable_session).await;
                log_status(SyncStatus::AuthFailed);
            }
            empty_collection_state_box()
        }
        Err(CollectionQueryError::Other(err)) => {
            if is_transient_transport_error(err) {
                *access_session = None;
                log_status(SyncStatus::TransportFailed);
            }
            empty_collection_state_box()
        }
    };

    publish_event(
        Event::RecommendationTopicContentUpdated {
            topic_slug: request.topic_slug,
            collection,
        },
        now_ms(),
    );
}

async fn handle_recommendation_access_error(
    err: RefreshError,
    current: &StartupCredential,
    access_session: &mut Option<ActiveAccessSession>,
    reusable_session: &mut Option<ReusableBackendSession<'_>>,
) {
    match err {
        RefreshError::Rejected(status) => {
            invalidate_access_state(access_session, reusable_session).await;
            log_status(SyncStatus::AuthFailed);
            warn!(
                "backend recommendation refresh rejected status={} source={}",
                status,
                current.source.label(),
            );
        }
        RefreshError::Other(err) => {
            *access_session = None;
            log_status(SyncStatus::TransportFailed);
            warn!("backend recommendation refresh failed: {:?}", err);
        }
    }
}

async fn handle_reader_pause_access_error(
    err: RefreshError,
    current: &StartupCredential,
    access_session: &mut Option<ActiveAccessSession>,
    reusable_session: &mut Option<ReusableBackendSession<'_>>,
) {
    match err {
        RefreshError::Rejected(status) => {
            invalidate_access_state(access_session, reusable_session).await;
            log_status(SyncStatus::AuthFailed);
            warn!(
                "backend reader pause refresh rejected status={} source={}",
                status,
                current.source.label(),
            );
        }
        RefreshError::Other(err) => {
            *access_session = None;
            log_status(SyncStatus::TransportFailed);
            warn!("backend reader pause refresh failed: {:?}", err);
        }
    }
}

async fn handle_prepare_content_request<'a>(
    context: BackendRequestContext<'a>,
    current: &mut StartupCredential,
    access_session: &mut Option<ActiveAccessSession>,
    reusable_session: &mut Option<ReusableBackendSession<'a>>,
    tls_session_cache: &mut Option<SerializedClientSession>,
    request: PrepareContentRequest,
) {
    if request.remote_item_id.is_empty() || request.content_id.is_empty() {
        return;
    }
    let operation_sync_id = next_sync_id();
    let operation_trace = TraceContext {
        sync_id: operation_sync_id,
        req_id: 0,
    };
    crate::memtrace!(
        "backend_sync",
        "component" = "backend",
        "at_ms" = now_ms(),
        "action" = "prepare_begin",
        "sync_id" = operation_sync_id,
        "req_id" = 0,
        "collection" = collection_label(request.collection),
        "content_id" = request.content_id.as_str(),
        "remote_item_id" = request.remote_item_id.as_str(),
        "remote_revision" = request.remote_revision,
    );

    if let Err(err) = ensure_access_session(
        context.stack,
        context.tls,
        context.ca_chain,
        context.tcp_state,
        current,
        access_session,
        reusable_session,
        tls_session_cache,
        operation_sync_id,
    )
    .await
    {
        match err {
            RefreshError::Rejected(status) => {
                crate::memtrace!(
                    "backend_sync",
                    "component" = "backend",
                    "at_ms" = now_ms(),
                    "action" = "prepare_auth_failed",
                    "sync_id" = operation_sync_id,
                    "req_id" = 0,
                    "status" = status,
                    "content_id" = request.content_id.as_str(),
                );
                log_status(SyncStatus::AuthFailed);
                warn!(
                    "backend content prepare refresh rejected status={} source={}",
                    status,
                    current.source.label(),
                );
                let _ = publish_package_state(
                    operation_trace,
                    request.collection,
                    request.remote_item_id,
                    PackageState::Failed,
                )
                .await;
            }
            RefreshError::Other(err) => {
                crate::memtrace!(
                    "backend_sync",
                    "component" = "backend",
                    "at_ms" = now_ms(),
                    "action" = "prepare_refresh_failed",
                    "sync_id" = operation_sync_id,
                    "req_id" = 0,
                    "error" = backend_error_label(err),
                    "content_id" = request.content_id.as_str(),
                );
                *access_session = None;
                log_status(SyncStatus::TransportFailed);
                warn!("backend content prepare refresh failed: {:?}", err);
                let _ = publish_package_state(
                    operation_trace,
                    request.collection,
                    request.remote_item_id,
                    prepare_error_package_state(err),
                )
                .await;
            }
        }
        return;
    }

    log_status(SyncStatus::SyncingContent);
    let access_token = access_session
        .as_ref()
        .map(|session| session.access_token.as_str())
        .unwrap_or("");

    match fetch_and_stage_package(
        context.stack,
        context.tls,
        context.ca_chain,
        context.tcp_client,
        access_token,
        reusable_session,
        tls_session_cache,
        request,
        operation_sync_id,
    )
    .await
    {
        Ok(result) => {
            let snapshot = *result.snapshot;
            publish_event(
                Event::CollectionContentUpdated(request.collection, Box::new(snapshot)),
                now_ms(),
            );
            crate::memtrace!(
                "backend_sync",
                "component" = "backend",
                "at_ms" = now_ms(),
                "action" = "prepare_cached",
                "sync_id" = operation_sync_id,
                "req_id" = 0,
                "collection" = collection_label(request.collection),
                "content_id" = request.content_id.as_str(),
                "remote_item_id" = request.remote_item_id.as_str(),
            );
            info!(
                "backend content cached collection={:?} content_id={}",
                request.collection,
                request.content_id.as_str(),
            );
            match result.opened {
                Ok(opened) => {
                    let total_units = opened.total_units;
                    let paragraph_count = opened.paragraphs.len();
                    let window_unit_count = opened.window.unit_count;
                    publish_event(
                        Event::ReaderContentOpened {
                            collection: request.collection,
                            content_id: request.content_id,
                            title: opened.title,
                            total_units,
                            paragraphs: opened.paragraphs,
                            window: opened.window,
                        },
                        now_ms(),
                    );
                    info!(
                        "backend content opened after prepare collection={:?} content_id={} total_units={} paragraph_count={} window_units={}",
                        request.collection,
                        request.content_id.as_str(),
                        total_units,
                        paragraph_count,
                        window_unit_count,
                    );
                    crate::memtrace!(
                        "backend_sync",
                        "component" = "backend",
                        "at_ms" = now_ms(),
                        "action" = "prepare_opened",
                        "sync_id" = operation_sync_id,
                        "req_id" = 0,
                        "collection" = collection_label(request.collection),
                        "content_id" = request.content_id.as_str(),
                        "remote_item_id" = request.remote_item_id.as_str(),
                        "total_units" = total_units,
                        "paragraph_count" = paragraph_count,
                        "window_units" = window_unit_count,
                    );
                }
                Err(err) => {
                    let _ = publish_package_state(
                        operation_trace,
                        request.collection,
                        request.remote_item_id,
                        PackageState::Failed,
                    )
                    .await;
                    warn!(
                        "backend content open after prepare failed collection={:?} content_id={} err={:?}",
                        request.collection,
                        request.content_id.as_str(),
                        err,
                    );
                }
            }
        }
        Err(PackagePrepareError::PendingRemote) => {
            crate::memtrace!(
                "backend_sync",
                "component" = "backend",
                "at_ms" = now_ms(),
                "action" = "prepare_pending_remote",
                "sync_id" = operation_sync_id,
                "req_id" = 0,
                "content_id" = request.content_id.as_str(),
            );
            let _ = publish_package_state(
                operation_trace,
                request.collection,
                request.remote_item_id,
                PackageState::PendingRemote,
            )
            .await;
            info!(
                "backend content pending remote collection={:?} content_id={}",
                request.collection,
                request.content_id.as_str(),
            );
        }
        Err(PackagePrepareError::Rejected(status)) => {
            crate::memtrace!(
                "backend_sync",
                "component" = "backend",
                "at_ms" = now_ms(),
                "action" = "prepare_rejected",
                "sync_id" = operation_sync_id,
                "req_id" = 0,
                "status" = status,
                "content_id" = request.content_id.as_str(),
            );
            if is_auth_status(status) {
                invalidate_access_state(access_session, reusable_session).await;
                log_status(SyncStatus::AuthFailed);
            }
            let _ = publish_package_state(
                operation_trace,
                request.collection,
                request.remote_item_id,
                PackageState::Failed,
            )
            .await;
            warn!("backend content fetch rejected status={}", status);
        }
        Err(PackagePrepareError::Other(err)) => {
            crate::memtrace!(
                "backend_sync",
                "component" = "backend",
                "at_ms" = now_ms(),
                "action" = "prepare_failed",
                "sync_id" = operation_sync_id,
                "req_id" = 0,
                "error" = backend_error_label(err),
                "content_id" = request.content_id.as_str(),
            );
            *access_session = None;
            let _ = publish_package_state(
                operation_trace,
                request.collection,
                request.remote_item_id,
                prepare_error_package_state(err),
            )
            .await;
            warn!("backend content fetch failed: {:?}", err);
        }
    }
}

async fn send_https_request<'a>(
    stack: Stack<'static>,
    tls: TlsReference<'a>,
    ca_chain: &Certificate<'static>,
    tcp_state: &'a BackendTcpClientState,
    tls_session_cache: &mut Option<SerializedClientSession>,
    request: HttpRequest<'_>,
    response_buffer: &'a mut [u8],
) -> Result<HttpResponse<'a>, BackendError> {
    // The second attempt only happens after the first attempt returned an error,
    // so no successful response still borrows the shared buffer.
    let response_buffer_ptr: *mut [u8] = response_buffer;
    let first_attempt = unsafe {
        send_https_request_once(
            stack,
            tls,
            ca_chain,
            tcp_state,
            tls_session_cache,
            request,
            &mut *response_buffer_ptr,
        )
        .await
    };
    match first_attempt {
        Err(err) if is_transient_transport_error(err) && TRANSPORT_RETRY_ATTEMPTS > 1 => {
            warn!(
                "backend request retry path={} attempt=1 err={:?}",
                request.path, err
            );
            Timer::after(Duration::from_millis(TRANSPORT_RETRY_BACKOFF_MS)).await;
            unsafe {
                send_https_request_once(
                    stack,
                    tls,
                    ca_chain,
                    tcp_state,
                    tls_session_cache,
                    request,
                    &mut *response_buffer_ptr,
                )
                .await
            }
        }
        other => other,
    }
}

async fn send_https_request_once<'a>(
    stack: Stack<'static>,
    tls: TlsReference<'a>,
    ca_chain: &Certificate<'static>,
    tcp_state: &'a BackendTcpClientState,
    tls_session_cache: &mut Option<SerializedClientSession>,
    request: HttpRequest<'_>,
    response_buffer: &'a mut [u8],
) -> Result<HttpResponse<'a>, BackendError> {
    let mut tcp_client = TcpClient::new(stack, tcp_state);
    tcp_client.set_timeout(Some(Duration::from_secs(
        request.class.socket_timeout_secs(),
    )));
    let ConnectedBackendSession {
        mut session,
        metrics,
        ..
    } = open_backend_session(
        stack,
        tls,
        ca_chain,
        &tcp_client,
        tls_session_cache,
        request.trace,
        request.path,
        request.class,
    )
    .await?;
    let response = send_https_request_over_session_with_metrics(
        &mut session,
        request,
        response_buffer,
        metrics,
    )
    .await;
    close_backend_tls_session(&mut session, "request").await;

    response
}

#[allow(clippy::too_many_arguments)]
async fn send_https_request_reusing_session<'a, 'b>(
    stack: Stack<'static>,
    tls: TlsReference<'a>,
    ca_chain: &Certificate<'static>,
    tcp_client: &'a BackendTcpClient<'a>,
    reusable_session: &mut Option<ReusableBackendSession<'a>>,
    tls_session_cache: &mut Option<SerializedClientSession>,
    request: HttpRequest<'_>,
    response_buffer: &'b mut [u8],
) -> Result<HttpResponse<'b>, BackendError> {
    let response_buffer_ptr: *mut [u8] = response_buffer;
    let first_attempt = unsafe {
        send_https_request_reusing_session_once(
            stack,
            tls,
            ca_chain,
            tcp_client,
            reusable_session,
            tls_session_cache,
            request,
            &mut *response_buffer_ptr,
        )
        .await
    };
    match first_attempt {
        Err(err) if is_transient_transport_error(err) && TRANSPORT_RETRY_ATTEMPTS > 1 => {
            close_reusable_session(reusable_session, "retry").await;
            warn!(
                "backend request retry path={} attempt=1 err={:?}",
                request.path, err
            );
            Timer::after(Duration::from_millis(TRANSPORT_RETRY_BACKOFF_MS)).await;
            unsafe {
                send_https_request_reusing_session_once(
                    stack,
                    tls,
                    ca_chain,
                    tcp_client,
                    reusable_session,
                    tls_session_cache,
                    request,
                    &mut *response_buffer_ptr,
                )
                .await
            }
        }
        other => other,
    }
}

#[allow(clippy::too_many_arguments)]
async fn send_https_request_reusing_session_once<'a, 'b>(
    stack: Stack<'static>,
    tls: TlsReference<'a>,
    ca_chain: &Certificate<'static>,
    tcp_client: &'a BackendTcpClient<'a>,
    reusable_session: &mut Option<ReusableBackendSession<'a>>,
    tls_session_cache: &mut Option<SerializedClientSession>,
    request: HttpRequest<'_>,
    response_buffer: &'b mut [u8],
) -> Result<HttpResponse<'b>, BackendError> {
    let metrics = ensure_reusable_session(
        stack,
        tls,
        ca_chain,
        tcp_client,
        reusable_session,
        tls_session_cache,
        request.trace,
        request.path,
        request.class,
    )
    .await?;
    let response = match reusable_session {
        Some(reusable) => {
            send_https_request_over_session_with_metrics(
                &mut reusable.session,
                request,
                response_buffer,
                metrics,
            )
            .await
        }
        None => unreachable!(),
    };

    update_reusable_session_after_buffered_request(reusable_session, request, &response).await;
    response
}

async fn send_https_request_over_session<'a, T>(
    session: &mut Session<'_, T>,
    request: HttpRequest<'_>,
    response_buffer: &'a mut [u8],
) -> Result<HttpResponse<'a>, BackendError>
where
    T: AsyncRead07 + AsyncWrite07,
{
    send_https_request_over_session_with_metrics(
        session,
        request,
        response_buffer,
        RequestMetrics::new(request.trace, true, request.class),
    )
    .await
}

async fn send_https_request_over_session_with_metrics<'a, T>(
    session: &mut Session<'_, T>,
    request: HttpRequest<'_>,
    response_buffer: &'a mut [u8],
    mut metrics: RequestMetrics,
) -> Result<HttpResponse<'a>, BackendError>
where
    T: AsyncRead07 + AsyncWrite07,
{
    write_http_request(
        session,
        request.class,
        request.path,
        request.method,
        request.content_type,
        request.bearer_token,
        request.body,
        request.connection_close,
    )
    .await?;
    log_request_phase(
        metrics.trace,
        request.path,
        request.class,
        "request_sent",
        metrics.elapsed_ms(),
    );
    let response = read_http_response(
        session,
        request.path,
        response_buffer,
        request.connection_close,
        &mut metrics,
    )
    .await;
    match &response {
        Ok(parsed) => {
            metrics.finish();
            log_request_timing(request, parsed.status, &metrics);
        }
        Err(_) => log_request_heap(request.path, "request failed"),
    }
    response
}

fn open_tls_session<'a, T>(
    tls: TlsReference<'a>,
    ca_chain: &Certificate<'static>,
    stream: T,
) -> Result<Session<'a, T>, BackendError>
where
    T: AsyncRead07 + AsyncWrite07,
{
    let mut config = ClientSessionConfig::new();
    config.ca_chain = Some(ca_chain.clone());
    config.server_name = Some(backend_host_cstr());
    // TLS 1.3 client hello key exchange is currently the failing allocation path on device
    // (`psa_export_public_key() -> MBEDTLS_ERR_SSL_ALLOC_FAILED`), so pin the device client
    // to TLS 1.2 until we can ship a lower-memory custom mbedTLS build.
    config.min_version = TlsVersion::Tls1_2;

    Session::new(tls, stream, &SessionConfig::Client(config)).map_err(|_| BackendError::Tls)
}

fn prepare_tls_session_resume<T>(
    session: &mut Session<'_, T>,
    tls_session_cache: &mut Option<SerializedClientSession>,
    path: &str,
    streaming: bool,
    metrics: &mut RequestMetrics,
) where
    T: AsyncRead07 + AsyncWrite07,
{
    let Some(cached_session_len) = tls_session_cache.as_ref().map(SerializedClientSession::len)
    else {
        return;
    };
    let resume_result = tls_session_cache
        .as_ref()
        .map(|cached_session| session.set_serialized_session(cached_session));

    match resume_result {
        Some(Ok(())) => {
            metrics.tls_resume_offered = true;
            info!(
                "backend tls session resume prepared path={} streaming={} bytes={}",
                path, streaming, cached_session_len,
            );
        }
        Some(Err(err)) => {
            info!(
                "backend tls session resume discarded path={} streaming={} err={:?}",
                path, streaming, err
            );
            *tls_session_cache = None;
        }
        None => {}
    }
}

fn discard_failed_tls_session_resume(
    tls_session_cache: &mut Option<SerializedClientSession>,
    path: &str,
    streaming: bool,
    metrics: &RequestMetrics,
) {
    if metrics.tls_resume_offered && tls_session_cache.take().is_some() {
        info!(
            "backend tls session resume discarded path={} streaming={} reason=handshake_failed",
            path, streaming
        );
    }
}

fn cache_negotiated_tls_session<T>(
    session: &Session<'_, T>,
    tls_session_cache: &mut Option<SerializedClientSession>,
    path: &str,
    streaming: bool,
) where
    T: AsyncRead07 + AsyncWrite07,
{
    match session.export_serialized_session() {
        Ok(cached_session) => {
            info!(
                "backend tls session cached path={} streaming={} bytes={}",
                path,
                streaming,
                cached_session.len(),
            );
            *tls_session_cache = Some(cached_session);
        }
        Err(err) => {
            info!(
                "backend tls session cache save failed path={} streaming={} err={:?}",
                path, streaming, err
            );
        }
    }
}

fn current_network_address(stack: Stack<'static>) -> Option<embassy_net::Ipv4Cidr> {
    stack.config_v4().map(|config| config.address)
}

fn is_backend_request_path_ready(stack: Stack<'static>) -> bool {
    stack.is_link_up()
        && current_network_address(stack).is_some()
        && crate::internet::backend_path_ready()
}
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
